hydroslide/tires_monitor/3d_parts/final parts/Power Input Box. lidstl.stl

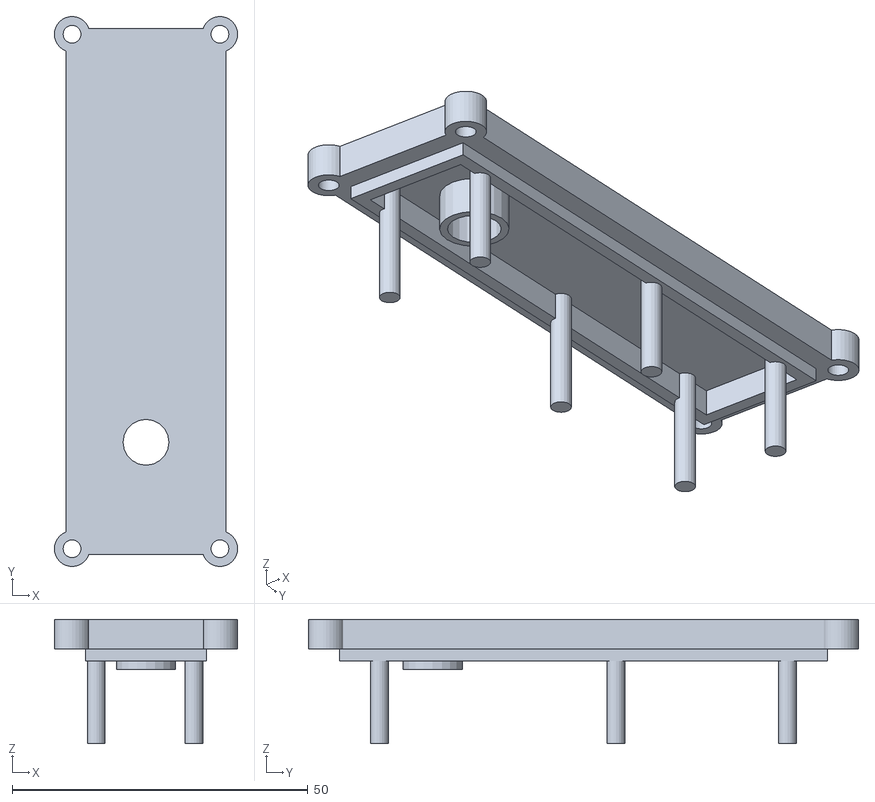
[picture p17: CAD file, 2025-01-14]
3d_parts/final parts/Power Input Box. lidstl.stl
31.0 x 93.0 x 21.0
