hydroslide/tires_monitor/3d_parts/final parts/display/Tire Temp Display Module high cup thick.stl

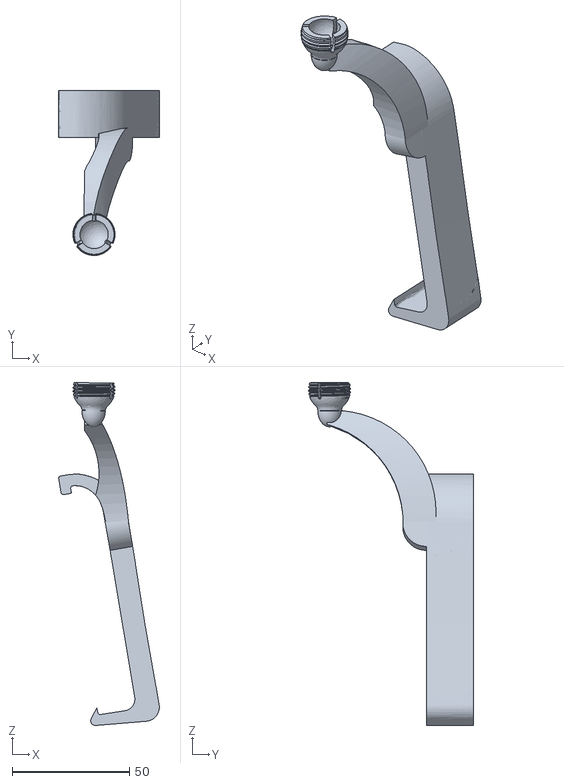
[picture p18: CAD file, 2025-01-14]
3d_parts/final parts/display/Tire Temp Display Module high cup thick.stl
42.9 x 70.4 x 146.2
