hydroslide/tires_monitor/3d_parts/final parts/Power Input Box button.stl

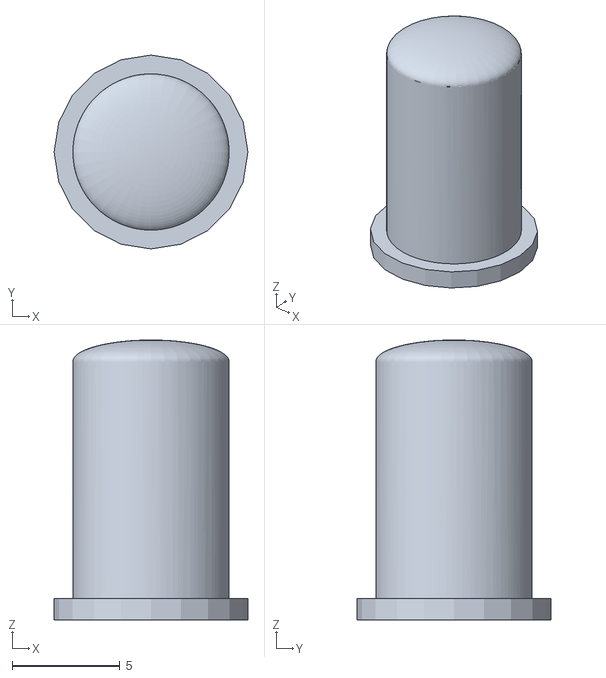
[picture p19: CAD file, 2025-01-14]
3d_parts/final parts/Power Input Box button.stl
9.00 x 9.00 x 13.0
