hydroslide/tires_monitor/3d_parts/final parts/display/Tire Temp Display Module ball.stl

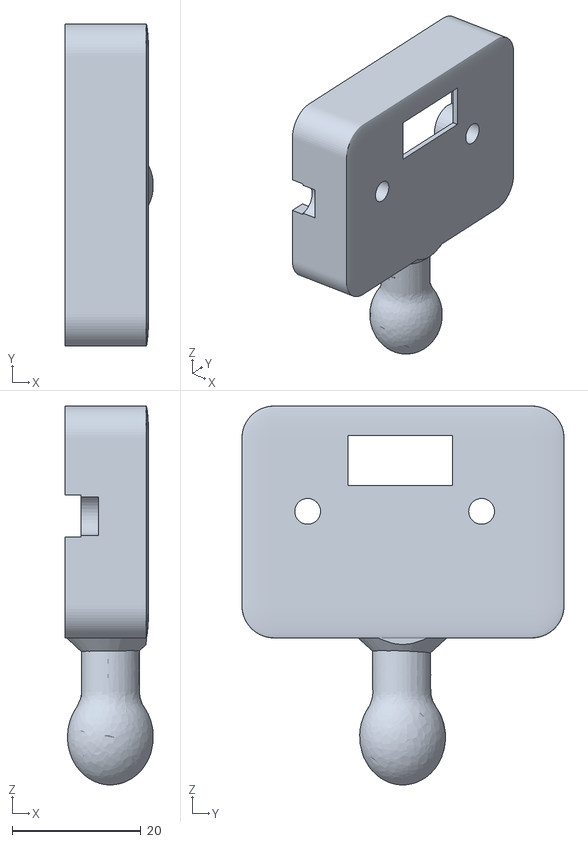
[picture p20: CAD file, 2025-01-14]
3d_parts/final parts/display/Tire Temp Display Module ball.stl
13.7 x 50.0 x 58.8
