hydroslide/tires_monitor/3d_parts/final parts/Tire Temp Sensor Box. protectionstl.stl

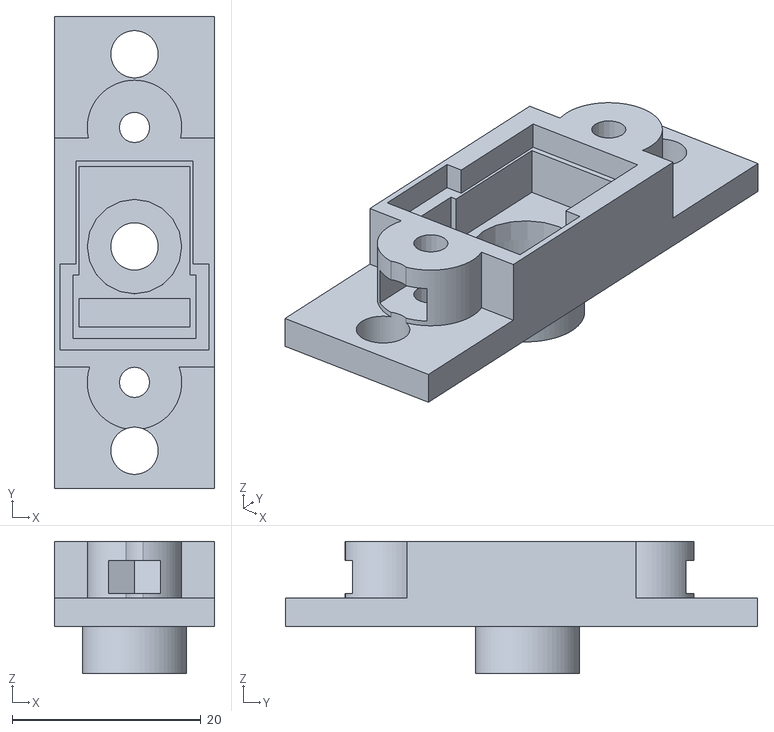
[picture p21: CAD file, 2025-01-14]
3d_parts/final parts/Tire Temp Sensor Box. protectionstl.stl
17.0 x 50.0 x 14.0
