hydroslide/tires_monitor/3d_parts/final parts/display/Tire Temp Display Module mount.stl

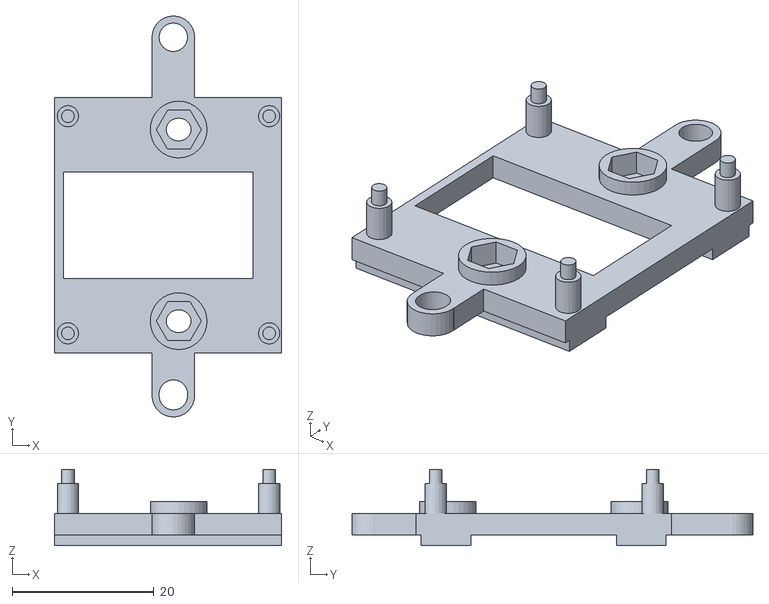
[picture p22: CAD file, 2025-01-14]
3d_parts/final parts/display/Tire Temp Display Module mount.stl
32.0 x 56.5 x 10.8
