hydroslide/tires_monitor/3d_parts/final parts/Tire Temp Sensor Lid.stl

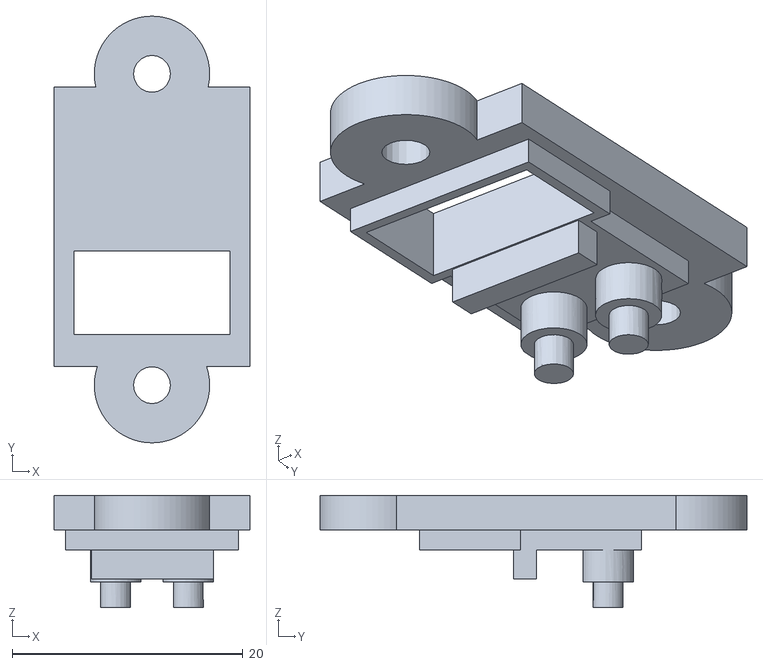
[picture p23: CAD file, 2024-12-06]
3d_parts/final parts/Tire Temp Sensor Lid.stl
17.0 x 37.0 x 9.75
