hydroslide/tires_monitor/3d_parts/final parts/display/Tire Temp Display Module ball mk2.stl

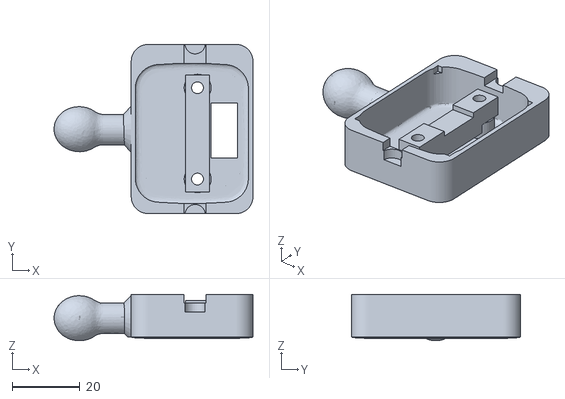
[picture p24: CAD file, 2025-01-14]
3d_parts/final parts/display/Tire Temp Display Module ball mk2.stl
58.8 x 50.0 x 13.7
