hydroslide/tires_monitor/3d_parts/final parts/display/Tire Temp Display Module strap new mk2.stl

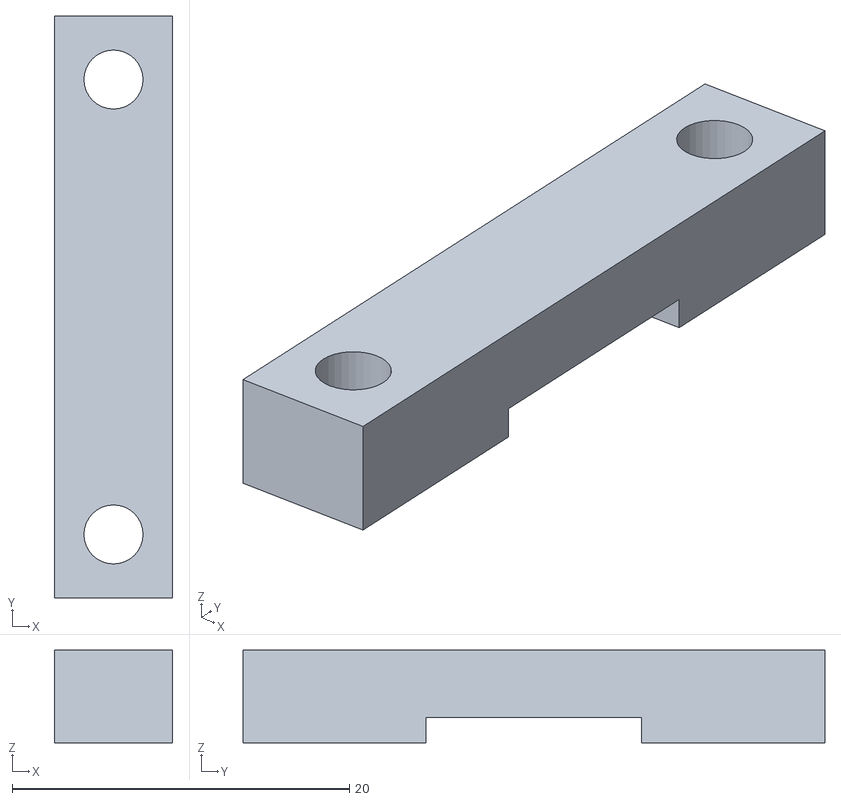
[picture p27: CAD file, 2025-01-14]
3d_parts/final parts/display/Tire Temp Display Module strap new mk2.stl
7.00 x 34.5 x 5.50
