hydroslide/tires_monitor/tires_esp32/Wheels.cpp

#include "Wheels.h"
#include "DisplayBase.h"
extern DisplayBase& display;

Wheels::Wheels(int _bufferPix,
               uint16_t _outlineColor,
               uint16_t _textColor,
               float _minTemp, float _idealTemp, float _maxTemp,
               char _tempUnit,
               bool _showSegmentDeltas, byte _minInflationDeltaPct, byte _minAlignmentDeltaPct,
               bool _fl3, bool _fr3, bool _rl3, bool _rr3,
               uint16_t _lowTempColor,    uint16_t _normalTempColor,
               uint16_t _idealTempColor,  uint16_t _highTempColor,
               uint16_t _lowTempTextColor,    uint16_t _normalTempTextColor,
               uint16_t _idealTempTextColor,  uint16_t _highTempTextColor)
  : bufferPix(_bufferPix), outlineColor(_outlineColor), textColor(_textColor),
    minTemp(_minTemp), idealTemp(_idealTemp), maxTemp(_maxTemp),
    tempUnit(_tempUnit),
    showSegmentDeltas(_showSegmentDeltas), minInflationDeltaPct(_minInflationDeltaPct), minAlignmentDeltaPct(_minAlignmentDeltaPct),
    fl3(_fl3), fr3(_fr3), rl3(_rl3), rr3(_rr3),
    lowTempColor(_lowTempColor), normalTempColor(_normalTempColor),
    idealTempColor(_idealTempColor), highTempColor(_highTempColor),
    lowTempTextColor(_lowTempTextColor), normalTempTextColor(_normalTempTextColor),
    idealTempTextColor(_idealTempTextColor), highTempTextColor(_highTempTextColor)
{
    int tireW  = (display.width()  - bufferPix*3) / 2;
    int tireH  = (display.height() - bufferPix*3) / 2;
    int x0 = bufferPix, x1 = x0 + tireW + bufferPix;
    int y0 = bufferPix, y1 = y0 + tireH + bufferPix;

    // lambda to pick class based on the bool
    auto mk = [&](bool three, int x, int y, byte index){
      if (three){
        ThreeSectionTire* tire = new ThreeSectionTire(x,y,tireW,tireH, bufferPix,
                                          outlineColor,textColor,tempUnit);
        tire->showSegmentDeltas = showSegmentDeltas;
        tire->minInflationDeltaPct = minInflationDeltaPct;
        tire->minAlignmentDeltaPct = minAlignmentDeltaPct;
        tire->tireIndex=index;
        return (Tire*)tire;
        }
      else
        return (Tire*)new Tire(x,y,tireW,tireH, bufferPix,
                               outlineColor,textColor,tempUnit);
    };

    frontLeft  = mk(fl3, x0,y0, 0);
    frontRight = mk(fr3, x1,y0, 1);
    rearLeft   = mk(rl3, x0,y1, 2);
    rearRight  = mk(rr3, x1,y1, 3);

    //   // Attempt to allocate frame buffer in PSRAM
    // framebuf = (uint16_t *)heap_caps_malloc(
    //     tft.width()* tft.height() * sizeof(uint16_t),
    //     MALLOC_CAP_SPIRAM
    // );
    // if (!framebuf) {
    //     // Fall back to normal heap
    //     framebuf = (uint16_t *)malloc(tft.width()* tft.height() * sizeof(uint16_t));
    // }
    // if (!framebuf) {
    //     // If allocation fails, halt
    //     while (true) { delay(1000); }
    // }


    // for (int yy = yStart; yy < yEnd; yy++) {
    //     for (int xx = xStart; xx < xEnd; xx++) {
    //         framebuf[yy * areaW + xx] = color;
    //     }
    //     // Yield to avoid watchdog reset
    //     //yield();
    // }
}

Wheels::Wheels(Wheels* src, bool _fl3, bool _fr3, bool _rl3, bool _rr3)
  : Wheels(
      src->bufferPix,
      src->outlineColor,
      src->textColor,
      src->minTemp, src->idealTemp, src->maxTemp,
      src->tempUnit,
      src->showSegmentDeltas, src->minInflationDeltaPct, src->minAlignmentDeltaPct,
      _fl3, _fr3, _rl3, _rr3,
      src->lowTempColor,
      src->normalTempColor,
      src->idealTempColor,
      src->highTempColor,
      src->lowTempTextColor,
      src->normalTempTextColor,
      src->idealTempTextColor,
      src->highTempTextColor
    )
{}

Wheels::~Wheels() {
    delete frontLeft;
    delete frontRight;
    delete rearLeft;
    delete rearRight;

    // if (framebuf) {
    //     free(framebuf);
    //     framebuf = nullptr;
    // }
}

void Wheels::draw(bool force, bool textOnly) {
    //RefreshScreen();
    if (flIsActive)
        frontLeft->draw(force, textOnly);
    if (frIsActive)
        frontRight->draw(force, textOnly);
    if (rlIsActive)        
        rearLeft->draw(force, textOnly);
    if (rrIsActive)
        rearRight->draw(force, textOnly);
}

void Wheels::RefreshScreen(){
        // Push the entire buffer to ST7789 at (areaX, areaY)
    // tft.startWrite();
    // tft.setAddrWindow(0, 0, tft.width(), tft.height());
    // tft.writePixels(framebuf, tft.width() * tft.height());
    // tft.endWrite();
}

void Wheels::setTireTemps(const TireTemps &fl,
                         const TireTemps &fr,
                         const TireTemps &rl,
                         const TireTemps &rr)
{
    struct P { Tire *t; const TireTemps &v; };
    P list[4] = {
      {frontLeft,  fl},
      {frontRight, fr},
      {rearLeft,   rl},
      {rearRight,  rr}
    };
    for (auto &p : list) {
      p.t->setTemps(p.v.values, p.v.count, (tempUnit=='F'),
                    minTemp, idealTemp, maxTemp,
                    lowTempColor, normalTempColor,
                    idealTempColor, highTempColor,
                    lowTempTextColor, normalTempTextColor,
                    idealTempTextColor, highTempTextColor);
    }
}

// Resolve a corner index to its ThreeSectionTire, or nullptr for a single-sensor corner.
// The fl3/fr3/rl3/rr3 flags stand in for RTTI, which this build doesn't have.
ThreeSectionTire* Wheels::cameraCorner(int corner) const {
    Tire* t;
    bool three;
    switch (corner) {
      case 0: t = frontLeft;  three = fl3; break;
      case 1: t = frontRight; three = fr3; break;
      case 2: t = rearLeft;   three = rl3; break;
      case 3: t = rearRight;  three = rr3; break;
      default: return nullptr;
    }
    return three ? static_cast<ThreeSectionTire*>(t) : nullptr;
}

void Wheels::setInflationVerdict(int corner, int8_t verdict) {
    ThreeSectionTire* ts = cameraCorner(corner);
    if (ts) ts->setInflationVerdict(verdict);
}

void Wheels::setDwellProgress(int corner, long score, long latch, long max) {
    ThreeSectionTire* ts = cameraCorner(corner);
    if (ts) ts->setDwellProgress(score, latch, max);
}

bool Wheels::cornerColors(int corner, uint16_t fill[3], uint16_t delta[3]) const {
    Tire* t;
    bool three;
    switch (corner) {
      case 0: t = frontLeft;  three = fl3; break;
      case 1: t = frontRight; three = fr3; break;
      case 2: t = rearLeft;   three = rl3; break;
      case 3: t = rearRight;  three = rr3; break;
      default: return false;
    }
    if (!three) return false;
    ThreeSectionTire* ts = static_cast<ThreeSectionTire*>(t);
    for (int i = 0; i < 3; i++) {
      fill[i]  = ts->sectionFillColor(i);
      delta[i] = ts->sectionDeltaColor(i);
    }
    return true;
}

    char Wheels::getTempUnit(){ return
     tempUnit;}
    void Wheels::setTempUnit(char _tempUnit){
        tempUnit=_tempUnit;
        frontLeft->tempUnit=tempUnit;
        frontRight->tempUnit=tempUnit;
        rearLeft->tempUnit=tempUnit;
        rearRight->tempUnit=tempUnit;
    }
