hydroslide/tires_monitor/tires_esp32/ThermalDisplay.cpp

#include "ThermalDisplay.h"
#include <esp_heap_caps.h>   // for heap_caps_malloc (PSRAM allocation)
#include <Arduino.h>         // for yield()
#include "TempReader.h"
#include <math.h>


extern HWCDC USBSerial;

// Define the static 256-entry color palette (RGB565)
const uint16_t ThermalDisplay::camColors[256] = {
  0x480F, 0x400F, 0x400F, 0x400F, 0x4010, 0x3810, 0x3810, 0x3810, 0x3810, 0x3010,
  0x3010, 0x3010, 0x2810, 0x2810, 0x2810, 0x2810, 0x2010, 0x2010, 0x2010, 0x1810,
  0x1810, 0x1811, 0x1811, 0x1011, 0x1011, 0x1011, 0x0811, 0x0811, 0x0811, 0x0011,
  0x0011, 0x0011, 0x0011, 0x0011, 0x0031, 0x0031, 0x0051, 0x0072, 0x0072, 0x0092,
  0x00B2, 0x00B2, 0x00D2, 0x00F2, 0x00F2, 0x0112, 0x0132, 0x0152, 0x0152, 0x0172,
  0x0192, 0x0192, 0x01B2, 0x01D2, 0x01F3, 0x01F3, 0x0213, 0x0233, 0x0253, 0x0253,
  0x0273, 0x0293, 0x02B3, 0x02D3, 0x02D3, 0x02F3, 0x0313, 0x0333, 0x0333, 0x0353,
  0x0373, 0x0394, 0x03B4, 0x03D4, 0x03D4, 0x03F4, 0x0414, 0x0434, 0x0454, 0x0474,
  0x0474, 0x0494, 0x04B4, 0x04D4, 0x04F4, 0x0514, 0x0534, 0x0534, 0x0554, 0x0554,
  0x0574, 0x0574, 0x0573, 0x0573, 0x0573, 0x0572, 0x0572, 0x0572, 0x0571, 0x0591,
  0x0591, 0x0590, 0x0590, 0x058F, 0x058F, 0x058F, 0x058E, 0x05AE, 0x05AE, 0x05AD,
  0x05AD, 0x05AD, 0x05AC, 0x05AC, 0x05AB, 0x05CB, 0x05CB, 0x05CA, 0x05CA, 0x05CA,
  0x05C9, 0x05C9, 0x05C8, 0x05E8, 0x05E8, 0x05E7, 0x05E7, 0x05E6, 0x05E6, 0x05E6,
  0x05E5, 0x05E5, 0x0604, 0x0604, 0x0604, 0x0603, 0x0603, 0x0602, 0x0602, 0x0601,
  0x0621, 0x0621, 0x0620, 0x0620, 0x0620, 0x0620, 0x0E20, 0x0E20, 0x0E40, 0x1640,
  0x1640, 0x1E40, 0x1E40, 0x2640, 0x2640, 0x2E40, 0x2E60, 0x3660, 0x3660, 0x3E60,
  0x3E60, 0x3E60, 0x4660, 0x4660, 0x4E60, 0x4E80, 0x5680, 0x5680, 0x5E80, 0x5E80,
  0x6680, 0x6680, 0x6E80, 0x6EA0, 0x76A0, 0x76A0, 0x7EA0, 0x7EA0, 0x86A0, 0x86A0,
  0x8EA0, 0x8EC0, 0x96C0, 0x96C0, 0x9EC0, 0x9EC0, 0xA6C0, 0xAEC0, 0xAEC0, 0xB6E0,
  0xB6E0, 0xBEE0, 0xBEE0, 0xC6E0, 0xC6E0, 0xCEE0, 0xCEE0, 0xD6E0, 0xD700, 0xDF00,
  0xDEE0, 0xDEC0, 0xDEA0, 0xDE80, 0xDE80, 0xE660, 0xE640, 0xE620, 0xE600, 0xE5E0,
  0xE5C0, 0xE5A0, 0xE580, 0xE560, 0xE540, 0xE520, 0xE500, 0xE4E0, 0xE4C0, 0xE4A0,
  0xE480, 0xE460, 0xEC40, 0xEC20, 0xEC00, 0xEBE0, 0xEBC0, 0xEBA0, 0xEB80, 0xEB60,
  0xEB40, 0xEB20, 0xEB00, 0xEAE0, 0xEAC0, 0xEAA0, 0xEA80, 0xEA60, 0xEA40, 0xF220,
  0xF200, 0xF1E0, 0xF1C0, 0xF1A0, 0xF180, 0xF160, 0xF140, 0xF100, 0xF0E0, 0xF0C0,
  0xF0A0, 0xF080, 0xF060, 0xF040, 0xF020, 0xF800
};

// ─── DEFINE & INITIALIZE STATICS ──────────────────────
// You can tweak these defaults, or rely on setTemperatureRange()
int ThermalDisplay::thresholdMin     = MINTEMP;
int ThermalDisplay::thresholdIdeal   = (MINTEMP + MAXTEMP) / 2;
int ThermalDisplay::thresholdMax     = MAXTEMP;

bool ThermalDisplay::useGradient = true;
bool ThermalDisplay::showPixelOffsets = false;

// Interactive crop-offset setup (#23); driven by OffsetSetup while that mode is up.
bool   ThermalDisplay::setupActive    = false;
int8_t ThermalDisplay::setupCorner    = -1;
bool   ThermalDisplay::setupRightSide = false;
bool   ThermalDisplay::setupBlinkOn   = true;
bool   ThermalDisplay::setupGuides    = true;   // cleared by LensSetup only (#31)

uint16_t ThermalDisplay::camPalette[256];
int      ThermalDisplay::lenCold;
int      ThermalDisplay::lenWarm;
int      ThermalDisplay::lenIdeal;
int      ThermalDisplay::lenHot;

// define+zero-init the static pointer:
uint16_t* ThermalDisplay::framebuf = nullptr;
TempReader* ThermalDisplay::tempReader = nullptr;

ThermalDisplay::ThermalDisplay(DisplayBase &displayTFT,
                               int areaX, int areaY,
                               int areaW, int areaH)
  : display(displayTFT),
    areaX(areaX), areaY(areaY), areaW(areaW), areaH(areaH)
{
    if (!framebuf){
        // Attempt to allocate frame buffer in PSRAM
        framebuf = (uint16_t *)heap_caps_malloc(
            areaW * areaH * sizeof(uint16_t),
            MALLOC_CAP_SPIRAM
        );
        if (!framebuf) {
            // Fall back to normal heap
            framebuf = (uint16_t *)malloc(areaW * areaH * sizeof(uint16_t));
        }
        if (!framebuf) {
            // If allocation fails, halt
            while (true) { delay(1000); }
        }
    }


}



ThermalDisplay::~ThermalDisplay() {
    if (framebuf) {
        free(framebuf);
        framebuf = nullptr;
    }
}

float ThermalDisplay::fahrenheitToCelsius(float f){
    return (f - 32.0f) * 5.0f / 9.0f;
}

// ─── STATIC THRESHOLD SETTER ──────────────────────────
void ThermalDisplay::setTemperatureRangeC(int minTemp,
                                         int idealTemp,
                                         int maxTemp)
{
    thresholdMin   = constrain(minTemp,   MINTEMP,   MAXTEMP);
    thresholdIdeal = constrain(idealTemp, thresholdMin, MAXTEMP);
    thresholdMax   = constrain(maxTemp,   thresholdIdeal, MAXTEMP);
    generatePalette();
}

void ThermalDisplay::setTemperatureRangeF(int minTemp,
                                         int idealTemp,
                                         int maxTemp)
{
    int minTempC = (int)fahrenheitToCelsius(minTemp);
    int idealTempC = (int)fahrenheitToCelsius(idealTemp);
    int maxTempC = (int)fahrenheitToCelsius(maxTemp);
    setTemperatureRangeC(minTempC, idealTempC, maxTempC);
}

/*
// ─── STATIC MAPPING HELPER ────────────────────────────
uint8_t ThermalDisplay::getColorIndexForTemp(int celsius) {
    // clamp within our class‐wide bounds
    celsius = constrain(celsius, thresholdMin, thresholdMax);

    // first half of palette = [thresholdMin…thresholdIdeal]
    if (celsius <= thresholdIdeal) {
        int upper = max(thresholdIdeal, thresholdMin + 1);
        int idx = map(celsius, thresholdMin, upper, 1, 127);
        return constrain(idx, 0, 127);
    }
    // second half        = (thresholdIdeal…thresholdMax]
    else {
        int lower = min(thresholdIdeal, thresholdMax - 1);
        int idx   = map(celsius, lower, thresholdMax, 128, 254);
        return constrain(idx, 128, 255);
    }
}
    */
uint8_t ThermalDisplay::getColorIndexForTemp(int c) {
    // clamp entire range: [min-7 … max+7]
    int lo = thresholdMin - 7;
    int hi = thresholdMax + 7;
    c = constrain(c, lo, hi);

    // pick which segment, then local map
    if (c <= thresholdMin) {
        // cold segment
        return map(c, lo, thresholdMin, 0, lenCold - 1);
    }
    else if (c <= thresholdIdeal) {
        // warm segment
        int start = lenCold;
        return start + map(c, thresholdMin, thresholdIdeal,
                           0, lenWarm - 1);
    }
    else if (c <= thresholdMax) {
        // ideal segment
        int start = lenCold + lenWarm;
        return start + map(c, thresholdIdeal, thresholdMax,
                           0, lenIdeal - 1);
    }
    else {
        // hot segment
        int start = lenCold + lenWarm + lenIdeal;
        return start + map(c, thresholdMax, hi,
                           0, lenHot - 1);
    }
}

static inline float _clamp360(float h) { 
  while (h < 0) h += 360.0f; 
  while (h >= 360.0f) h -= 360.0f; 
  return h; 
}

void ThermalDisplay::rgb2hsv(uint8_t R,uint8_t G,uint8_t B, float& h,float& s,float& v) {
  float r = R/255.0f, g = G/255.0f, b = B/255.0f;
  float maxv = fmaxf(r,fmaxf(g,b)), minv = fminf(r,fminf(g,b));
  v = maxv;
  float d = maxv - minv;
  s = (maxv == 0.0f) ? 0.0f : d / maxv;
  if (d == 0.0f) { h = 0.0f; return; }
  if (maxv == r)      h = 60.0f * fmodf(((g - b) / d), 6.0f);
  else if (maxv == g) h = 60.0f * (((b - r) / d) + 2.0f);
  else                h = 60.0f * (((r - g) / d) + 4.0f);
  if (h < 0) h += 360.0f;
}

void ThermalDisplay::hsv2rgb888(float h,float s,float v, uint8_t& R,uint8_t& G,uint8_t& B) {
  h = _clamp360(h);
  float c = v * s;
  float hh = (h / 60.0f);
  float x = c * (1.0f - fabsf(fmodf(hh, 2.0f) - 1.0f));
  float r=0,g=0,b=0;
  if      (0<=hh && hh<1){ r=c; g=x; b=0; }
  else if (1<=hh && hh<2){ r=x; g=c; b=0; }
  else if (2<=hh && hh<3){ r=0; g=c; b=x; }
  else if (3<=hh && hh<4){ r=0; g=x; b=c; }
  else if (4<=hh && hh<5){ r=x; g=0; b=c; }
  else                   { r=c; g=0; b=x; }
  float m = v - c;
  r += m; g += m; b += m;
  R = (uint8_t)lroundf(r*255.0f);
  G = (uint8_t)lroundf(g*255.0f);
  B = (uint8_t)lroundf(b*255.0f);
}

uint16_t ThermalDisplay::interpolateHSV_saturated(uint16_t c1, uint16_t c2, float t) {
  if (t <= 0.0f) return c1;
  if (t >= 1.0f) return c2;

  uint8_t r1,g1,b1, r2,g2,b2;
  rgb565_to_888(c1, r1,g1,b1);
  rgb565_to_888(c2, r2,g2,b2);

  float h1,s1,v1, h2,s2,v2;
  rgb2hsv(r1,g1,b1, h1,s1,v1);
  rgb2hsv(r2,g2,b2, h2,s2,v2);

  // shortest-path hue interpolation
  float dh = fmodf((h2 - h1 + 540.0f), 360.0f) - 180.0f; // [-180,180]
  float h  = _clamp360(h1 + t * dh);

  // fully saturated rim (S=1, V=1) inside band
  uint8_t R,G,B;
  hsv2rgb888(h, 1.0f, 1.0f, R,G,B);
  return rgb888_to_565(R,G,B);
}

uint16_t ThermalDisplay::interpolateDesaturateToTarget(uint16_t cStart, uint16_t cEnd, float t) {
  if (t <= 0.0f) return cStart;
  if (t >= 1.0f) return cEnd;

  uint8_t rs,gs,bs, re,ge,be;
  rgb565_to_888(cStart, rs,gs,bs);
  rgb565_to_888(cEnd,   re,ge,be);

  float hs,ss,vs, he,se,ve;
  rgb2hsv(rs,gs,bs, hs,ss,vs);
  rgb2hsv(re,ge,be, he,se,ve);

  // hold hue at start, ramp S: 1 → se, and V: vs → ve
  float s = 1.0f + (se - 1.0f) * t;
  float v = vs    + (ve - vs)  * t;

  uint8_t R,G,B;
  hsv2rgb888(hs, s, v, R,G,B);
  return rgb888_to_565(R,G,B);
}

/*
void ThermalDisplay::generatePalette() {
    // 1/8th for “hot” (red→white) = 32 entries
    lenHot = 256 / 8;       // = 32
    int rest = 256 - lenHot; // = 224

    // degree spans
    int spanCold = 7;                         // fixed
    int spanWarm = thresholdIdeal - thresholdMin;
    int spanIdeal= thresholdMax   - thresholdIdeal;
    int sumRest = spanCold + spanWarm + spanIdeal;

    // allocate the other three segment lengths proportionally
    lenCold  = max(1, int(round((float)spanCold  / sumRest * rest)));
    lenWarm  = max(1, int(round((float)spanWarm  / sumRest * rest)));
    // ensure we fill exactly 'rest'
    lenIdeal = rest - lenCold - lenWarm;

    // now carve into camPalette[]
    int idx = 0;

    // ── cold: violet → cyan
    for (int i = 0; i < lenCold; ++i) {
        float t = float(i) / (lenCold - 1);
        if (useGradient)
            camPalette[idx++] = interpolate565(COLOR_COLD_START, COLOR_CYAN, t);
        else
            camPalette[idx++] = COLOR_COLD;
    }
    // ── warm: cyan → yellow-orange
    for (int i = 0; i < lenWarm; ++i) {
        float t = float(i) / (lenWarm - 1);
        if (useGradient)
            camPalette[idx++] = interpolate565(COLOR_CYAN, COLOR_ORANGE, t);// COLOR_YELLOW_ORANGE, t);
        else
            camPalette[idx++] = COLOR_WARM;
    }
    // ── ideal: yellow-orange → red
    int lastI = 0;
    int halfIdeal = lenIdeal/2;
    for (int i = 0; i < halfIdeal; ++i) {
        float t = float(i) / (halfIdeal - 1);
        if (useGradient)
            camPalette[idx++] = interpolate565(COLOR_ORANGE, COLOR_PURPLE, t);//interpolate565(COLOR_YELLOW_ORANGE, COLOR_RED, t);
        else
            camPalette[idx++] = COLOR_PURPLE;//COLOR_IDEAL;
    }

    halfIdeal = lenIdeal-halfIdeal;
    for (int i =0; i < halfIdeal; ++i) {
        float t = float(i) / (halfIdeal - 1);
        if (useGradient)
            camPalette[idx++] = interpolate565(COLOR_PURPLE, COLOR_PURPLE_HOT, t);//interpolate565(COLOR_YELLOW_ORANGE, COLOR_RED, t);
        else
            camPalette[idx++] = COLOR_PURPLE;//COLOR_IDEAL;
    }


    // ── hot: red → white (always 32 entries)
    for (int i = 0; i < lenHot; ++i) {
        float t = float(i) / (lenHot - 1);
        if (useGradient)
            camPalette[idx++] = interpolate565(COLOR_PURPLE_HOT, COLOR_HOT, t); //interpolate565(COLOR_RED, COLOR_WHITE, t);
        else
            camPalette[idx++] = COLOR_HOT;
    }
}
    */

void ThermalDisplay::generatePalette() {
  // 1/8th for “hot” tail
  lenHot = 256 / 8;                 // 32
  int rest = 256 - lenHot;          // 224

  // degree spans (unchanged)
  int spanCold  = 7;
  int spanWarm  = thresholdIdeal - thresholdMin;
  int spanIdeal = thresholdMax   - thresholdIdeal;
  int sumRest   = spanCold + spanWarm + spanIdeal;

  lenCold  = max(1, int(lroundf((float)spanCold  / sumRest * rest)));
  lenWarm  = max(1, int(lroundf((float)spanWarm  / sumRest * rest)));
  lenIdeal =           rest - lenCold - lenWarm;

  auto t_of = [](int i, int n) -> float {
    return (n > 1) ? (float)i / (float)(n - 1) : 0.0f;
  };

  int idx = 0;

  // COLD: violet → cyan (HSV saturated)
  for (int i = 0; i < lenCold; ++i) {
    float t = t_of(i, lenCold);
    camPalette[idx++] = useGradient
      ? interpolateHSV_saturated(COLOR_COLD_START, COLOR_CYAN, t)
      : COLOR_COLD;
  }

  // WARM: cyan → orange (HSV saturated)
  for (int i = 0; i < lenWarm; ++i) {
    float t = t_of(i, lenWarm);
    camPalette[idx++] = useGradient
      ? interpolateHSV_saturated(COLOR_CYAN, COLOR_ORANGE, t)
      : COLOR_WARM;
  }

  // IDEAL (split in half, as you already do):
  //   orange → purple (HSV saturated)
  int halfIdealA = lenIdeal / 2;
  for (int i = 0; i < halfIdealA; ++i) {
    float t = t_of(i, halfIdealA);
    camPalette[idx++] = useGradient
      ? interpolateHSV_saturated(COLOR_ORANGE, COLOR_PURPLE, t)
      : COLOR_PURPLE; // your solid fallback
  }

  //   purple → purple_hot (HSV saturated)
  int halfIdealB = lenIdeal - halfIdealA;
  for (int i = 0; i < halfIdealB; ++i) {
    float t = t_of(i, halfIdealB);
    camPalette[idx++] = useGradient
      ? interpolateHSV_saturated(COLOR_PURPLE, COLOR_PURPLE_HOT, t)
      : COLOR_PURPLE; // your solid fallback
  }

  // HOT: purple_hot → hot (desaturate toward your target color)
  for (int i = 0; i < lenHot; ++i) {
    float t = t_of(i, lenHot);
    camPalette[idx++] = useGradient
      ? interpolateDesaturateToTarget(COLOR_PURPLE_HOT, COLOR_HOT, t)
      : COLOR_HOT;
  }

  // Safety: ensure we filled exactly 256
  // (harmless if idx==256; clamps if rounding created an off-by-one)
  while (idx < 256) camPalette[idx++] = camPalette[255];
}


uint16_t ThermalDisplay::interpolate565(uint16_t c1,
                                        uint16_t c2,
                                        float t)
{
    // extract 5/6/5 bits
    int r1 = (c1 >> 11) & 0x1F,  g1 = (c1 >> 5) & 0x3F,  b1 = c1 & 0x1F;
    int r2 = (c2 >> 11) & 0x1F,  g2 = (c2 >> 5) & 0x3F,  b2 = c2 & 0x1F;
    // linear interp
    int r = r1 + (r2 - r1) * t + 0.5f;
    int g = g1 + (g2 - g1) * t + 0.5f;
    int b = b1 + (b2 - b1) * t + 0.5f;
    // re-pack
    return (uint16_t)((r << 11) | (g << 5) | b);
}


void ThermalDisplay::setTempIndex(int _tempIndex){                                        
        tempIndex = _tempIndex;
    }

void ThermalDisplay::updateDisplay(){
   updateDisplay(tempIndex);
}

void ThermalDisplay::updateDisplay(int _tempIndex){
     if (isActive && tempReader->tireSensorIsCamera[_tempIndex])
        updateDisplay(tempReader->tire_frames[_tempIndex], _tempIndex);
}

/*
void ThermalDisplay::updateDisplay(const int temps[CAMERA_WIDTH * CAMERA_HEIGHT], int _tempIndex)
{
    // Build the areaW×areaH RGB565 buffer from 32×24 temps[]
    for (int camY = 0; camY < CAMERA_HEIGHT; camY++) {
        for (int camX = 0; camX < CAMERA_WIDTH; camX++) {
            int idxFlat = camY * CAMERA_WIDTH + camX;

            int raw = temps[idxFlat];
            // clamp using our static min/max
            //raw = constrain(raw, thresholdMin, thresholdMax);

            uint8_t ci      = getColorIndexForTemp(raw);
            uint16_t color  = camPalette[ci];//camColors[ci];
           
            // Compute scaled block in areaW×areaH
            int xStart = (camX     * areaW) / CAMERA_WIDTH;
            int xEnd   = ((camX+1) * areaW) / CAMERA_WIDTH;
            int yStart = (camY     * areaH) / CAMERA_HEIGHT;
            int yEnd   = ((camY+1) * areaH) / CAMERA_HEIGHT;

            for (int yy = yStart; yy < yEnd; yy++) {
                for (int xx = xStart; xx < xEnd; xx++) {
                    framebuf[yy * areaW + xx] = color;
                }
                // Yield to avoid watchdog reset
                //yield();
            }
        }
    }

    // Push the entire buffer to display at (areaX, areaY)
    display.pushPixels(areaX, areaY, areaW, areaH, framebuf, areaW * areaH);

    if (showPixelOffsets)
        drawPixelOffsets(_tempIndex);
}
*/

void ThermalDisplay::updateDisplay(const int temps[CAMERA_WIDTH * CAMERA_HEIGHT], int _tempIndex)
{
    // When showPixelOffsets == false, we *stretch* only the X range between the two offsets
    // to fill the entire display width. Y mapping is unchanged.
    int leftOff  = 0;
    int rightOff = 0;
    int cropW    = CAMERA_WIDTH;
    // Offset setup (#23) always shows the FULL frame regardless of the Show Offsets setting:
    // a guide drawn over an image that has already been cropped to those same offsets is a
    // line down the edge of the screen saying nothing. You can only aim a crop against the
    // uncropped picture.
    const bool stretchX = !showPixelOffsets && !setupActive;

    if (stretchX) {
        // Read the per-sensor offsets
        leftOff  = (int)tempReader->leftPixelOffset[_tempIndex];
        rightOff = (int)tempReader->rightPixelOffset[_tempIndex];

        // Sanity checks to avoid degenerate/invalid ranges
        if (leftOff   < 0) leftOff = 0;
        if (rightOff  < 0) rightOff = 0;
        if (leftOff + rightOff >= CAMERA_WIDTH) { // pathological; disable stretch
            leftOff = 0; rightOff = 0;
        }
        cropW = CAMERA_WIDTH - leftOff - rightOff;
        if (cropW <= 0) cropW = 1; // hard guard against div-by-zero
    }

    // Build the areaW×areaH RGB565 buffer from 32×24 temps[]
    for (int camY = 0; camY < CAMERA_HEIGHT; camY++) {
        // Y scaling is unchanged regardless of stretch
        const int yStart = (camY     * areaH) / CAMERA_HEIGHT;
        const int yEnd   = ((camY+1) * areaH) / CAMERA_HEIGHT;

        // X loop: either full width or the cropped range
        const int xBegin = stretchX ? leftOff : 0;
        const int xFinal = CAMERA_WIDTH - (stretchX ? rightOff : 0);

        for (int camX = xBegin; camX < xFinal; camX++) {
            const int idxFlat = camY * CAMERA_WIDTH + camX;

            // A pixel the lens correction has no source data for is painted BLACK, never
            // run through the palette (#31). getColorIndexForTemp() clamps its input into
            // the threshold range, so every possible int comes back as a real temperature
            // colour -- a placeholder value would render as a confident reading. Cold-end
            // navy would read as "cold background"; hot-end (0xFF9F, near-white) would
            // read as a scorching tire. Black is already this display's "nothing here"
            // (it is what a corner with no camera shows), and it is in no palette.
            uint16_t color;
            if (!TempReader::lensPixelValid(idxFlat)) {
                color = ST77XX_BLACK;
            } else {
                int raw = temps[idxFlat];
                uint8_t ci = getColorIndexForTemp(raw);
                color = camPalette[ci];
            }

            // Compute scaled block in areaW×areaH
            // If stretching, remap localX (camX - leftOff) across cropW → full areaW.
            // If not stretching, localX == camX and cropW == CAMERA_WIDTH (original behavior).
            const int localX = stretchX ? (camX - leftOff) : camX;

            const int xStart = (localX     * areaW) / cropW;
            const int xEnd   = ((localX+1) * areaW) / cropW;

            for (int yy = yStart; yy < yEnd; yy++) {
                uint16_t* row = &framebuf[yy * areaW];
                for (int xx = xStart; xx < xEnd; xx++) {
                    row[xx] = color;
                }
            }
        }
    }

    // Push the entire buffer to display at (areaX, areaY)
    display.pushPixels(areaX, areaY, areaW, areaH, framebuf, areaW * areaH);

    // When not stretching (i.e., showPixelOffsets == true, or offset setup owns the screen),
    // draw the guide lines on top. setupGuides is the one exception: Set Camera Degrees
    // (#31) borrows setupActive for its full-frame view but wants no guides over it.
    if ((showPixelOffsets || setupActive) && setupGuides)
        drawPixelOffsets(_tempIndex);
}


void ThermalDisplay::drawPixelOffsets(int _tempIndex){
    byte leftOffset = tempReader->leftPixelOffset[_tempIndex];
    byte rightOffset = tempReader->rightPixelOffset[_tempIndex];

    // Setup mode draws BOTH guides unconditionally (#23). Outside it the >0 guard stays: a
    // zero-offset guide lands hard against the image edge and is just clutter when nobody is
    // aiming the camera. While aiming it is the opposite -- an invisible line is one you
    // cannot walk back out from zero.
    const bool always = setupActive;

    // Which guide, if either, is the value being edited. -1 means nothing is armed (the
    // confirm screens), so every line sits steady.
    const bool armedHere = setupActive && (setupCorner == (int8_t)_tempIndex);

    if(leftOffset >0 || always){
        int leftX = (((leftOffset * areaW) / CAMERA_WIDTH)-1)+areaX;
        drawOffsetGuide(leftX, armedHere && !setupRightSide);
    }

    if (rightOffset >0 || always){
        int rightX = ((areaW- ((rightOffset * areaW) / CAMERA_WIDTH))+1)+areaX;
        drawOffsetGuide(rightX, armedHere && setupRightSide);
    }

}

// One crop guide.
//
// Every pixel is clamped into the image rectangle, because that rectangle -- and only that
// rectangle -- is re-blitted on the next update. A line drawn in the bezel margin (which is
// where the arithmetic above puts a 0 offset) would never be erased, so it would smear as
// the value moved and the blink would have nothing to blink against.
void ThermalDisplay::drawOffsetGuide(int x, bool armed){
    const int lo = areaX;
    const int hi = areaX + areaW - 1;

    if (x < lo) x = lo;
    if (x > hi) x = hi;

    // The dark half of the blink draws nothing at all: the next frame's blit is the erase,
    // so there is no second color to paint and no flicker in the image underneath.
    if (armed && !setupBlinkOn) return;

    // The armed guide is 3 px wide so it is unmistakable at arm's length in daylight -- it
    // is the only thing on screen saying which of the eight values a swipe will move.
    const int half = armed ? 1 : 0;
    for (int gx = x - half; gx <= x + half; gx++){
        if (gx >= lo && gx <= hi)
            display.drawFastVLine(gx, areaY, areaH, OFFSET_LINE_COLOR);
    }
}
