hydroslide/tires_monitor/tires_esp32/TireMenu.cpp

#include "TireMenu.h"
#include "MenuRenderer.h"
#include "TireProfiles.h"
#include "TempReader.h"
#include "OffsetSetup.h"
#include "LensSetup.h"

extern MenuRenderer menuRenderer;
// The live reader, owned by the sketch. Only "Set Offsets" (#23) and "Set Camera Degrees"
// (#31) read it here, and only to ask whether any corner has a camera worth aiming.
extern TempReader* tempReader;

// ----------------------------------------------------
//  1) Global variables for each setting
// ----------------------------------------------------

//
// -- Enums --
static uint8_t currentMode = 0; // 0=Street, 1=Track
static const char* currentModeLabels[] = {"Street", "Track"};

static uint8_t temperatureScale = 0; // 0=Farenheit, 1=Celsius
static const char* tempScaleLabels[] = {"F", "C"};

static uint8_t nightBrightness   = 25;

// -- Per-mode default tire profile (#14) --
// A mode no longer carries its own temp window; it names the tire profile it starts from,
// and the profile is the single source of truth for Min/Ideal/Max (plus K / tau / crop).
// Both are enum indices into the profile slots: Street -> EC02 (1), Track -> ECF (0).
static uint8_t streetProfile = 1;
static uint8_t trackProfile  = 0;

// -- Street tire temp window (#27) --
// Street gets its own Min/Ideal/Max back, and in Street mode it OVERRIDES the active
// profile's window. #14 was right that two windows for the same tire is redundant on
// track -- but street is not the same tire problem. A street window is not a tuning
// target, it is a "are these anywhere near warm" scale, and it has to stay put while you
// swap between profiles that are all tuned for track heat. Pinning it to a profile meant
// either editing that profile's window (breaking it for track) or keeping a decoy
// "street" profile whose K/tau/crop you did not actually want.
//
// So this overrides ONLY the window. K, tau and the camera crop offsets still come from
// the active profile in both modes -- nothing else carries them -- which is why the
// Street "Default Profile" above still matters in Street mode.
//
// The values are the pre-#14 Street window, unchanged: 40/120/160 in the same F-seed
// convention TireProfile.window* uses (stored as F, displayed/converted per Temperature
// Scale). Track is untouched and still reads the profile.
//
// Off is a real position: it falls straight back to the active profile's window, which is
// exactly the post-#14 behavior, so this can be A/B'd against the profile without
// retyping the numbers.
static bool    streetWindowEnabled = true;
static uint8_t streetMin           = 40;
static uint8_t streetIdeal         = 120;
static uint8_t streetMax           = 160;

// -- Calculated display mode (story 03; Track-mode only) --
// 0=Raw surface, 1=Calculated (EMA_tau(surface)+K carcass estimate).
static uint8_t calcDisplayMode = 0;
static const char* calcDisplayModeLabels[] = {"Raw", "Calculated"};

// -- Balance summary show/hide (story 05; Track-mode only) --
// Governs whether the front/rear + left/right balance readout is offered. When off the
// "Balance" summary item reports that it is hidden instead of opening.
static bool showBalance = true;

// -- Auto-seal on stationary (story 01; Track-mode only) --
// When on, a running session self-seals after a sustained still period (a backstop for
// a forgotten swipe-to-end). Best-effort IMU-stillness only (no speed channel), so it
// defaults off.
static bool autoSealStationary = false;

// -- Hardware Temp Sensor Indices -- REMOVED (#22)
// Four menu-editable, EEPROM-persisted bytes (addrs 20/22/24/26) that nothing ever read:
// there was no getter, and the real mux map is the hardcoded sensorIndices{0, 7, 3, 4} in
// TempReader's constructor. They presented as a working sensor remap and were not one, so
// the whole "Hardware Settings" branch went with them. The addresses are simply no longer
// walked by save/load; the stale bytes are inert, which is why this needed no magic bump.

// -- Camera Offsets --
// Per-corner crop offsets are no longer globals (#15): they live in TireProfile, are
// edited under Tire Profiles -> Offsets, and are read back through the accessors at the
// bottom of this file. "Camera Settings" keeps only the device-wide display toggles.

static bool useThermalGradient = true;
static bool testEnabled = true;
static bool showPixelOffsets = true;
static bool highFrequencyUpdates = false;

// -- Fisheye lens correction (#31) --
// Device-wide, not per-profile: this describes the LENS, one rig with four identical
// ones, so it has nothing to do with which tire is fitted.
//
// lensFovDegrees is the field of view across the 32-pixel width, fed straight into the
// re-projection. 110 is the wide-angle MLX90640's datasheet figure and the right place to
// start, but the real lens is not exactly equidistant -- which is why the value is tunable
// from the car via "Set Camera Degrees" rather than being a constant.
//
// lensFitToView chooses what happens to the rows the correction has no data for: off
// letterboxes them black (honest, and it shows you what the correction is costing), on
// squashes the image vertically to fill the frame (keeps lines straight, drops aspect
// ratio). Defaults OFF so the cost is visible while you are still finding the FOV.
static bool    lensCorrectEnabled = true;
static uint8_t lensFovDegrees     = 110;
static bool    lensFitToView      = false;
static bool showSegmentDeltas = false;
static uint8_t minInflationDeltaPct = 10;
static uint8_t minAlignmentDeltaPct = 15;

// -- IMU capture gate (global; story 02) --
// Two dwells live here and they are NOT the same thing (#20):
//   gateDwellTenths  -- how long the car must hold sub-threshold lateral g before we
//                       start CAPTURING. 0 reproduces the pre-#20 instant behavior.
//   alertDwellTenths -- how long an over/under condition must persist on already-captured
//                       frames before the inflation verdict LATCHES.
static bool    imuGateEnabled       = true; // suppress reads while cornering
static bool    showGateBar          = true; // on-screen lateral-g test bar (#20)
static uint8_t lateralGateCentiG    = 35;   // |lateral g| threshold, centi-g (0.35 g)
static uint8_t gateDwellTenths      = 5;    // capture dwell, tenths of a second (0.5 s)
static uint8_t alertDwellTenths     = 25;   // latch dwell, tenths of a second (2.5 s)
static uint8_t imuOrient            = 0;    // lateral-axis map: 0=Auto,1=X,2=Y,3=Z
static const char* imuOrientLabels[] = {"Auto", "X", "Y", "Z"};


// ----------------------------------------------------
//  2) MenuValueBindings
// ----------------------------------------------------
static MenuValueBinding currentModeBinding = {
    VALUE_ENUM,
    &currentMode,
    nullptr,
    0, // minByte
    0, // maxByte
    0, // eepromAddress (or -1 if ignoring)
    currentModeLabels,
    2  // enumCount
};

static MenuValueBinding temperatureScaleBinding = {
    VALUE_ENUM,
    &temperatureScale,
    nullptr,
    0,
    0,
    2, // eepromAddress or -1
    tempScaleLabels,
    2
};

// Night Brightenss
static MenuValueBinding nightBrightnessBinding = {
    VALUE_BYTE,
    &nightBrightness,
    nullptr,
    0,
    100,
    28,
    nullptr,
    0
};

// Per-mode default tire profile (#14). Persisted at two of the addresses freed by the
// removed Street/Track Min/Ideal/Max bytes (6 and 8); the rest (10, 14, 16, 18) were free
// until #27 claimed all four (see below). The labels are the live profile slot names, so
// renaming a profile renames the choices here too.
static MenuValueBinding streetProfileBinding = {
    VALUE_ENUM,
    &streetProfile,
    nullptr,
    0,
    0,
    6,
    g_profileNameLabels,
    PROFILE_COUNT
};

static MenuValueBinding trackProfileBinding = {
    VALUE_ENUM,
    &trackProfile,
    nullptr,
    0,
    0,
    8,
    g_profileNameLabels,
    PROFILE_COUNT
};

// Street tire temp window (#27). These reclaim the last four bytes #14 freed: 10 was the
// old streetMax, 14/16/18 the old trackMin/Ideal/Max. Reusing them is safe only because
// SETTINGS_MAGIC is bumped alongside -- a block saved by #14..#26 firmware never WROTE
// these four, so they still hold whatever a pre-#14 save left there, and
// loadMenuFromEEPROMHelper() copies bytes in verbatim with no min/max clamping. Without
// the bump a stale trackMax=180 at 18 would load as streetWindowEnabled=true and a stale
// trackMin=100 at 14 as the Street ideal. See MenuSystem.cpp.
//
// Same 0..255 range as the profile window fields: the window is a raw F-seed byte, and
// clamping min <= ideal <= max is the display's job (ThermalDisplay::setTemperatureRangeC),
// not the menu's -- so the ordering rule stays in exactly one place.
static MenuValueBinding streetWindowEnabledBinding = {
    VALUE_BOOL,
    &streetWindowEnabled,
    nullptr,
    0,
    0,
    18,
    nullptr,
    0
};

static MenuValueBinding streetMinBinding = {
    VALUE_BYTE,
    &streetMin,
    nullptr,
    0,
    255,
    10,
    nullptr,
    0
};

static MenuValueBinding streetIdealBinding = {
    VALUE_BYTE,
    &streetIdeal,
    nullptr,
    0,
    255,
    14,
    nullptr,
    0
};

static MenuValueBinding streetMaxBinding = {
    VALUE_BYTE,
    &streetMax,
    nullptr,
    0,
    255,
    16,
    nullptr,
    0
};

// Calculated display mode (EEPROM addr 1; free byte, magic-sentinel load makes 0 safe)
static MenuValueBinding calcDisplayModeBinding = {
    VALUE_ENUM,
    &calcDisplayMode,
    nullptr,
    0,
    0,
    1,
    calcDisplayModeLabels,
    2
};

// Balance summary show/hide (EEPROM addr 49; free byte between the menu bindings and
// the tire-profile region at 50+). The magic-sentinel load makes the false/0 case safe.
static MenuValueBinding showBalanceBinding = {
    VALUE_BOOL,
    &showBalance,
    nullptr,
    0,
    0,
    49,
    nullptr,
    0
};

// Auto-seal on stationary (EEPROM addr 3; free byte among the menu bindings). The
// magic-sentinel load makes the false/0 case safe.
static MenuValueBinding autoSealStationaryBinding = {
    VALUE_BOOL,
    &autoSealStationary,
    nullptr,
    0,
    0,
    3,
    nullptr,
    0
};

static MenuValueBinding useThermalGradientBinding = {
    VALUE_BOOL,
    &useThermalGradient,
    nullptr,
    0,
    0,
    30,
    nullptr,
    0
};

// EEPROM 31..38 used to hold the eight global camera offsets. #15 moved the offsets into
// the tire profile (persisted verbatim in the profile region), so 31 was re-purposed for
// the inflation indicator (see below) and 32..38 are now free.

static MenuValueBinding showPixelOffsetsBinding = {
    VALUE_BOOL,
    &showPixelOffsets,
    nullptr,
    0,
    0,
    39,
    nullptr,
    0
};

// Lens correction (#31). EEPROM 34/35/36, out of the run of bytes #15 freed and #20 took
// 32/33 from. No earlier firmware ever WROTE these, and loadMenuFromEEPROMHelper() copies
// stored bytes in verbatim with no min/max clamping -- a stale 0xFF at 34 would land as a
// 255-degree field of view and build a degenerate map on the first boot. SETTINGS_MAGIC is
// bumped alongside so the block re-seeds from the compiled-in defaults instead.
static MenuValueBinding lensCorrectEnabledBinding = {
    VALUE_BOOL,
    &lensCorrectEnabled,
    nullptr,
    0,
    0,
    35,
    nullptr,
    0
};
static MenuValueBinding lensFovDegreesBinding = {
    VALUE_BYTE,
    &lensFovDegrees,
    nullptr,
    60,    // below this the correction is doing nothing worth the resample
    140,   // above this the centre is de-magnified >2.2x and a fifth of the frame is dead;
           // the map degenerates entirely at 180 (rectilinear focal length -> 0)
    34,
    nullptr,
    0
};
static MenuValueBinding lensFitToViewBinding = {
    VALUE_BOOL,
    &lensFitToView,
    nullptr,
    0,
    0,
    36,
    nullptr,
    0
};

static MenuValueBinding testEnabledBinding = {
    VALUE_BOOL,
    &testEnabled,
    nullptr,
    0,
    0,
    40,
    nullptr,
    0
};
static MenuValueBinding highFrequencyUpdatesBinding = {
    VALUE_BOOL,
    &highFrequencyUpdates,
    nullptr,
    0,
    0,
    41,
    nullptr,
    0
};
static MenuValueBinding showSegmentDeltasBinding = {
    VALUE_BOOL,
    &showSegmentDeltas,
    nullptr,
    0,
    0,
    42,
    nullptr,
    0
};

static MenuValueBinding minInflationDeltaPctBinding = {
    VALUE_BYTE,
    &minInflationDeltaPct,
    nullptr,
    0,
    16,
    43,
    nullptr,
    0
};
static MenuValueBinding minAlignmentDeltaPctBinding = {
    VALUE_BYTE,
    &minAlignmentDeltaPct,
    nullptr,
    0,
    16,
    44,
    nullptr,
    0
};

// IMU capture gate test bar + capture dwell (#20). These take EEPROM 32 and 33 out of the
// run of bytes #15 freed. Because no earlier firmware ever WROTE 32/33, a stored settings
// block from before #20 holds junk there, and loadMenuFromEEPROMHelper() copies bytes in
// verbatim with no min/max clamping -- a stale 0xFF would land as a 25.5 s capture dwell.
// SETTINGS_MAGIC is bumped alongside this so the first boot after the flash re-seeds from
// the compiled-in defaults instead.
static MenuValueBinding gateDwellTenthsBinding = {
    VALUE_BYTE,
    &gateDwellTenths,
    nullptr,
    0,    // 0.0 s -- instant capture, the pre-#20 behavior
    50,   // 5.0 s
    32,
    nullptr,
    0
};
static MenuValueBinding showGateBarBinding = {
    VALUE_BOOL,
    &showGateBar,
    nullptr,
    0,
    0,
    33,
    nullptr,
    0
};

// IMU capture gate settings (EEPROM 45..48; magic-sentinel load makes 0 safe)
static MenuValueBinding imuGateEnabledBinding = {
    VALUE_BOOL,
    &imuGateEnabled,
    nullptr,
    0,
    0,
    45,
    nullptr,
    0
};
static MenuValueBinding lateralGateCentiGBinding = {
    VALUE_BYTE,
    &lateralGateCentiG,
    nullptr,
    10,   // 0.10 g
    100,  // 1.00 g
    46,
    nullptr,
    0
};
static MenuValueBinding alertDwellTenthsBinding = {
    VALUE_BYTE,
    &alertDwellTenths,
    nullptr,
    5,    // 0.5 s
    100,  // 10 s
    47,
    nullptr,
    0
};
static MenuValueBinding imuOrientBinding = {
    VALUE_ENUM,
    &imuOrient,
    nullptr,
    0,
    0,
    48,
    imuOrientLabels,
    4
};

// EEPROM 31 is FREE again as of #21, which removed the "Inflation" toggle. No magic bump
// is needed for a removal alone: no binding reads 31 any more, so a stale byte there is
// simply never loaded. Bump only if something later CLAIMS 31.

// -- Tire profiles (story 04) --
// The selector and all edit fields bind to TireProfiles globals. Since #14 the selector
// is TRANSIENT (EEPROM_NO_PERSIST): the active slot is always resolved from the current
// mode's default profile at boot and on every mode change, so persisting a "last profile"
// would only fight that. A manual pick here still takes effect immediately and holds
// until the next mode change or reboot.
//
// Since #15 every edit field below is TRANSIENT too -- they are never tree-walked to
// EEPROM. They used to be duplicated at bytes 113..121, but #15 grew TireProfile so three
// slots run past there. The duplicate is gone rather than relocated: the profile region
// already stores these byte-verbatim, so there was never anything worth persisting twice.
// Dropping it also spares the offset fields the menu path's "a VALUE_BYTE stored as 0 is
// ambiguous" history (see MenuSystem.cpp).
//
// #19: these bind DIRECTLY into the selected slot (g_profiles[g_profileSel]) -- there is no
// working copy any more. retargetProfileBindings() re-points them when the selection
// changes, so switching profiles only changes which slot the UI edits; every slot keeps its
// own pending edits, and root "Save Settings" writes them all. The initialisers below name
// slot 0 purely to start from a valid address (a link-time constant -- no static-init-order
// hazard); the first retarget happens before the menu can be drawn.
static MenuValueBinding profileSelectBinding = {
    VALUE_ENUM,
    &g_profileSel,
    nullptr,
    0,
    0,
    EEPROM_NO_PERSIST,
    g_profileNameLabels,
    PROFILE_COUNT
};
static MenuValueBinding profileWindowMinBinding = {
    VALUE_BYTE, &g_profiles[0].windowMin, nullptr, 0, 255, EEPROM_NO_PERSIST, nullptr, 0
};
static MenuValueBinding profileWindowIdealBinding = {
    VALUE_BYTE, &g_profiles[0].windowIdeal, nullptr, 0, 255, EEPROM_NO_PERSIST, nullptr, 0
};
static MenuValueBinding profileWindowMaxBinding = {
    VALUE_BYTE, &g_profiles[0].windowMax, nullptr, 0, 255, EEPROM_NO_PERSIST, nullptr, 0
};
static MenuValueBinding profileOffsetKBinding = {
    VALUE_BYTE, &g_profiles[0].offsetK, nullptr, 0, 80, EEPROM_NO_PERSIST, nullptr, 0
};
static MenuValueBinding profileTauBinding = {
    VALUE_BYTE, &g_profiles[0].tauSeconds, nullptr, 1, 60, EEPROM_NO_PERSIST, nullptr, 0
};
// Per-corner camera crop offsets (#15), corner order FL, FR, RL, RR. Same edit-buffer /
// transient treatment as the fields above; the range mirrors the old global offsets.
static MenuValueBinding profileLeftOffsetFLBinding = {
    VALUE_BYTE, &g_profiles[0].leftOffset[0], nullptr, 0, PROFILE_OFFSET_MAX, EEPROM_NO_PERSIST, nullptr, 0
};
static MenuValueBinding profileRightOffsetFLBinding = {
    VALUE_BYTE, &g_profiles[0].rightOffset[0], nullptr, 0, PROFILE_OFFSET_MAX, EEPROM_NO_PERSIST, nullptr, 0
};
static MenuValueBinding profileLeftOffsetFRBinding = {
    VALUE_BYTE, &g_profiles[0].leftOffset[1], nullptr, 0, PROFILE_OFFSET_MAX, EEPROM_NO_PERSIST, nullptr, 0
};
static MenuValueBinding profileRightOffsetFRBinding = {
    VALUE_BYTE, &g_profiles[0].rightOffset[1], nullptr, 0, PROFILE_OFFSET_MAX, EEPROM_NO_PERSIST, nullptr, 0
};
static MenuValueBinding profileLeftOffsetRLBinding = {
    VALUE_BYTE, &g_profiles[0].leftOffset[2], nullptr, 0, PROFILE_OFFSET_MAX, EEPROM_NO_PERSIST, nullptr, 0
};
static MenuValueBinding profileRightOffsetRLBinding = {
    VALUE_BYTE, &g_profiles[0].rightOffset[2], nullptr, 0, PROFILE_OFFSET_MAX, EEPROM_NO_PERSIST, nullptr, 0
};
static MenuValueBinding profileLeftOffsetRRBinding = {
    VALUE_BYTE, &g_profiles[0].leftOffset[3], nullptr, 0, PROFILE_OFFSET_MAX, EEPROM_NO_PERSIST, nullptr, 0
};
static MenuValueBinding profileRightOffsetRRBinding = {
    VALUE_BYTE, &g_profiles[0].rightOffset[3], nullptr, 0, PROFILE_OFFSET_MAX, EEPROM_NO_PERSIST, nullptr, 0
};

// ----------------------------------------------------
//  3) Submenu Item Arrays
// ----------------------------------------------------
// -- "Temperature": the two global decisions about what a temperature number IS (#22) --
// "Source" is the old root-level "Display" (Raw/Calculated). It was surfaced in both mode
// menus (#16), which read as a per-mode setting; it is neither per-mode NOR a display
// setting. It is one shared global byte, and per TempReader.h it REPLACES the working
// section temps with EMA_tau(surface)+K -- so the inflation verdict, the balance readout,
// session recording and the primary NBP channels all run on whichever signal is picked
// here. Filing it under "Display" would repeat exactly the mislabel this menu fixes.
// "Scale" is the old root-level "Temp Scale"; it is a pure unit conversion and is buried
// here because it is set once and never touched again.
static MenuItem temperatureMenu[] = {
    { "Source", MENU_VALUE, nullptr, nullptr, 0, &calcDisplayModeBinding  },
    { "Scale",  MENU_VALUE, nullptr, nullptr, 0, &temperatureScaleBinding }
};

// Balance summary action (defined in section 6). Opens the front/rear + left/right
// readout; Track-mode-only and honors the Show Balance toggle.
static void doShowBalance();
// Session summary recall action (story 01). Opens the last sealed summary; Track-only.
static void doViewSummary();

// Street's own tire temp window (#27) joins Default Profile here -- this is the "obvious
// home for the next per-mode setting" the #22 comment left room for, and the window is
// the one thing street genuinely wants to hold independently of whichever track-tuned
// profile happens to be active.
//
// "Override Window" leads the three values it governs: with it off they are inert and the
// active profile's window applies, which is the post-#14 behavior. Track Settings
// deliberately gets no equivalent -- on track the profile IS the window.
static MenuItem streetSettingsMenu[] = {
    { "Default Profile", MENU_VALUE, nullptr, nullptr, 0, &streetProfileBinding      },
    { "Override Window", MENU_VALUE, nullptr, nullptr, 0, &streetWindowEnabledBinding },
    { "Min",             MENU_VALUE, nullptr, nullptr, 0, &streetMinBinding          },
    { "Ideal",           MENU_VALUE, nullptr, nullptr, 0, &streetIdealBinding        },
    { "Max",             MENU_VALUE, nullptr, nullptr, 0, &streetMaxBinding          }
};

static MenuItem trackSettingsMenu[] = {
    { "Default Profile", MENU_VALUE, nullptr,      nullptr, 0, &trackProfileBinding    },
    { "Show Balance", MENU_VALUE,  nullptr,        nullptr, 0, &showBalanceBinding     },
    { "Balance",      MENU_ACTION, doShowBalance,  nullptr, 0, nullptr                 },
    { "View Summary", MENU_ACTION, doViewSummary,  nullptr, 0, nullptr                 },
    { "Auto-Seal",    MENU_VALUE,  nullptr,        nullptr, 0, &autoSealStationaryBinding }
};

static MenuItem modeSettingsMenu[] = {
    { "Street Settings", MENU_SUBMENU, nullptr, streetSettingsMenu, sizeof(streetSettingsMenu)/sizeof(MenuItem), nullptr },
    { "Track Settings",  MENU_SUBMENU, nullptr, trackSettingsMenu,  sizeof(trackSettingsMenu)/sizeof(MenuItem),  nullptr }
};

// -- "Straight-Line Gate": was "IMU Gate" (#22) --
// Renamed off the chip and onto the job. These four decide which frames are allowed to
// count at all, so they gate the INPUT to the verdict; they are set-up values (Orientation
// especially) rather than things tuned between sessions, which is why they sit one level
// below the thresholds instead of beside them.
//
// The two dwells are still NOT the same thing, and they are now deliberately on separate
// screens with names that say so: "Gate Dwell" here is how long the car must hold
// sub-threshold lateral g before capture STARTS; "Latch" on the parent screen is how long
// a verdict must hold on already-captured frames before it TRIPS. See the block comment on
// the backing variables.
static MenuItem straightLineGateMenu[] = {
    { "Gate Enable",     MENU_VALUE, nullptr, nullptr, 0, &imuGateEnabledBinding   },
    { "Lateral cg",      MENU_VALUE, nullptr, nullptr, 0, &lateralGateCentiGBinding },
    { "Gate Dwell 0.1s", MENU_VALUE, nullptr, nullptr, 0, &gateDwellTenthsBinding   },
    { "Orientation",     MENU_VALUE, nullptr, nullptr, 0, &imuOrientBinding         },
};

// -- "Inflation & Camber": one feature, one menu (#22) --
// These nine settings are a single pipeline -- thresholds -> straight-line gate -> latch ->
// paint it -- but they used to be split across "IMU Gate" (6) and "Camera Settings" (3),
// and not one of those three had anything to do with a camera. Named for the two things the
// check distinguishes: edge-vs-centre divergence is an inflation call, outer-vs-inner is a
// camber one. What you actually tune sits on this screen; the gate mechanics nest below.
static MenuItem inflationCamberMenu[] = {
    { "Segment Deltas",    MENU_VALUE, nullptr, nullptr, 0, &showSegmentDeltasBinding },
    { "Show G Bar",        MENU_VALUE, nullptr, nullptr, 0, &showGateBarBinding       },
    { "Inflation Delta %", MENU_VALUE, nullptr, nullptr, 0, &minInflationDeltaPctBinding },
    { "Alignment Delta %", MENU_VALUE, nullptr, nullptr, 0, &minAlignmentDeltaPctBinding },
    { "Latch 0.1s",        MENU_VALUE, nullptr, nullptr, 0, &alertDwellTenthsBinding  },
    { "Straight-Line Gate", MENU_SUBMENU, nullptr, straightLineGateMenu, sizeof(straightLineGateMenu)/sizeof(MenuItem), nullptr }
};

// -- "Display": what is left once the mislabelled items go home (#22) --
// The old "Camera Settings" was named for hardware and held three verdict settings that
// have moved to Inflation & Camber. What genuinely remains is presentation: how bright the
// screen is at night, how the thermal image is coloured, whether the crop guides are drawn
// over it, and how often the tire display repaints.
// Interactive lens setup action (#31), defined in section 6.
static void doSetCameraDegrees();

// The four lens items (#31) join it on the same "device-wide, so it lives here" rule that
// already put Show Offsets here rather than next to the per-profile offset values. They
// are not purely presentation -- the correction changes measured band temperatures, not
// just the picture -- but the root menu is an exact 9/9 fit against MenuRenderer's
// viewport and a 10th root item brings the scrollbar back, so a "Camera" root submenu
// would have to displace something.
//
// This menu is now 8 of 9 rows. The NEXT item added here brings the scrollbar back, at
// which point the four lens items should nest into a "Lens" submenu rather than anything
// being displaced.
static MenuItem displayMenu[] = {
    { "Night Brightness", MENU_VALUE, nullptr, nullptr, 0, &nightBrightnessBinding      },
    { "Thermal Gradient", MENU_VALUE, nullptr, nullptr, 0, &useThermalGradientBinding   },
    { "Show Offsets",     MENU_VALUE, nullptr, nullptr, 0, &showPixelOffsetsBinding     },
    { "Hi Freq Updates",  MENU_VALUE, nullptr, nullptr, 0, &highFrequencyUpdatesBinding },
    { "Lens Correct",     MENU_VALUE, nullptr, nullptr, 0, &lensCorrectEnabledBinding   },
    { "Camera Degrees",   MENU_VALUE, nullptr, nullptr, 0, &lensFovDegreesBinding       },
    { "Fit to View",      MENU_VALUE, nullptr, nullptr, 0, &lensFitToViewBinding        },
    { "Set Camera Degrees", MENU_ACTION, doSetCameraDegrees, nullptr, 0, nullptr        }
};

// Per-profile camera crop offsets (#15). Mirrors the corner / Left-Right shape the old
// global "Camera Settings" offsets had, so the tuning gestures are unchanged -- only the
// values now belong to the selected profile's edit buffer, saved by "Save Prof".
static MenuItem profileOffsetsFrontLeftMenu[] = {
    { "Left",  MENU_VALUE, nullptr, nullptr, 0, &profileLeftOffsetFLBinding  },
    { "Right", MENU_VALUE, nullptr, nullptr, 0, &profileRightOffsetFLBinding }
};

static MenuItem profileOffsetsFrontRightMenu[] = {
    { "Left",  MENU_VALUE, nullptr, nullptr, 0, &profileLeftOffsetFRBinding  },
    { "Right", MENU_VALUE, nullptr, nullptr, 0, &profileRightOffsetFRBinding }
};

static MenuItem profileOffsetsRearLeftMenu[] = {
    { "Left",  MENU_VALUE, nullptr, nullptr, 0, &profileLeftOffsetRLBinding  },
    { "Right", MENU_VALUE, nullptr, nullptr, 0, &profileRightOffsetRLBinding }
};

static MenuItem profileOffsetsRearRightMenu[] = {
    { "Left",  MENU_VALUE, nullptr, nullptr, 0, &profileLeftOffsetRRBinding  },
    { "Right", MENU_VALUE, nullptr, nullptr, 0, &profileRightOffsetRRBinding }
};

// Interactive setup action (#23), defined in section 6.
static void doSetOffsets();

// "Set Offsets" leads because it is the way these values are meant to be set: the eight
// numeric fields below it are a pixel aim, and this screen is the only one that shows you
// the picture you are aiming at. They stay for fine adjustment and for reading back what the
// mode left behind.
static MenuItem profileOffsetsMenu[] = {
    { "Set Offsets", MENU_ACTION, doSetOffsets, nullptr, 0, nullptr },
    { "Front Left",  MENU_SUBMENU, nullptr, profileOffsetsFrontLeftMenu,  sizeof(profileOffsetsFrontLeftMenu)/sizeof(MenuItem),  nullptr },
    { "Front Right", MENU_SUBMENU, nullptr, profileOffsetsFrontRightMenu, sizeof(profileOffsetsFrontRightMenu)/sizeof(MenuItem), nullptr },
    { "Rear Left",   MENU_SUBMENU, nullptr, profileOffsetsRearLeftMenu,   sizeof(profileOffsetsRearLeftMenu)/sizeof(MenuItem),   nullptr },
    { "Rear Right",  MENU_SUBMENU, nullptr, profileOffsetsRearRightMenu,  sizeof(profileOffsetsRearRightMenu)/sizeof(MenuItem),  nullptr }
};

// Tire-profile action callbacks (defined in section 6).
static void doNameProfile();
static void doResetProfile();

// No "Load" / "Save Prof" items (#18). The fields below edit the selected slot directly
// (#19), so there is nothing to load by hand; and the root menu's "Save Settings" writes
// all three slots, so a profile-only save was a strict subset of it -- and a misleading one
// once several profiles can hold pending edits at the same time. "Reset" stays -- reverting
// one slot to its seed is distinct.
static MenuItem tireProfilesMenu[] = {
    { "Profile",   MENU_VALUE,  nullptr,        nullptr, 0, &profileSelectBinding     },
    { "Name",      MENU_ACTION, doNameProfile,  nullptr, 0, nullptr                   },
    { "Min",       MENU_VALUE,  nullptr,        nullptr, 0, &profileWindowMinBinding  },
    { "Ideal",     MENU_VALUE,  nullptr,        nullptr, 0, &profileWindowIdealBinding},
    { "Max",       MENU_VALUE,  nullptr,        nullptr, 0, &profileWindowMaxBinding  },
    // Display names only (#17) -- the fields stay offsetK / tauSeconds in code. "\xF8" is
    // the CP437 degree ring; display.cp437(true) in setup() makes it render literally.
    { "Carcass Offset \xF8", MENU_VALUE, nullptr, nullptr, 0, &profileOffsetKBinding   },
    { "Carcass Lag s", MENU_VALUE,  nullptr,        nullptr, 0, &profileTauBinding     },
    { "Offsets",   MENU_SUBMENU, nullptr, profileOffsetsMenu, sizeof(profileOffsetsMenu)/sizeof(MenuItem), nullptr },
    { "Reset",     MENU_ACTION, doResetProfile, nullptr, 0, nullptr                   },
};

// ----------------------------------------------------
//  4) Save/Load Action Callbacks
// ----------------------------------------------------
static void doSave();
static void doLoad();

// ----------------------------------------------------
//  5) Main Menu Definition (with Save/Load items)
// ----------------------------------------------------
// Root menu (#22). Exactly 9 items against MenuRenderer's 9-row viewport
// ((240 - 22 status strip - 30 top margin) / 20), so it fills the screen without
// scrolling -- it was 11, and scrolled. That is an exact fit with no headroom: a 10th
// root item brings the scrollbar back, so anything added later has to displace something
// or nest. Grouped on one rule -- no menu is named after the hardware it happens to use --
// which is why "Camera Settings", "IMU Gate" and "Hardware Settings" are all gone.
//
// "Current Tire" is a second item pointing at the SAME profileSelectBinding as
// Tire Profiles -> Profile, hoisted to the root so swapping tires is one tap. It needs no
// supporting code: serviceProfileEditSync() polls g_profileSel from loop() rather than
// hooking a particular menu item, so it fires whichever of the two wrote it. The binding is
// EEPROM_NO_PERSIST, so the duplicate reference cannot double-write.
static MenuItem mainMenu[] = {
    {
      "Current Mode",
      MENU_VALUE,
      nullptr,
      nullptr,
      0,
      &currentModeBinding
    },
    {
      "Current Tire",
      MENU_VALUE,
      nullptr,
      nullptr,
      0,
      &profileSelectBinding
    },
    {
      "Temperature",
      MENU_SUBMENU,
      nullptr,
      temperatureMenu,
      sizeof(temperatureMenu)/sizeof(MenuItem),
      nullptr
    },
    {
      "Mode Settings",
      MENU_SUBMENU,
      nullptr,
      modeSettingsMenu,
      sizeof(modeSettingsMenu)/sizeof(MenuItem),
      nullptr
    },
    {
      "Tire Profiles",
      MENU_SUBMENU,
      nullptr,
      tireProfilesMenu,
      sizeof(tireProfilesMenu)/sizeof(MenuItem),
      nullptr
    },
    {
      "Inflation & Camber",
      MENU_SUBMENU,
      nullptr,
      inflationCamberMenu,
      sizeof(inflationCamberMenu)/sizeof(MenuItem),
      nullptr
    },
    {
      "Display",
      MENU_SUBMENU,
      nullptr,
      displayMenu,
      sizeof(displayMenu)/sizeof(MenuItem),
      nullptr
    },
    {
        "Test",
        MENU_VALUE,
        nullptr,
        nullptr,
        0,
        &testEnabledBinding
    },
    {
      "Save Config",
      MENU_ACTION,
      doSave,
      nullptr,
      0,
      nullptr
    }
};

// We create a global MenuSystem instance for all items
static MenuSystem tireMenuSystem(
    mainMenu,
    sizeof(mainMenu)/sizeof(MenuItem)
);

// ----------------------------------------------------
//  6) Implementation of the Save/Load callbacks
// ----------------------------------------------------
static void doSave()
{
    tireMenuSystem.saveToEEPROM();
    // Persist tire profiles alongside the menu settings so one "Save Settings" covers
    // everything. Since #19 the edit fields write straight into their slot, so there is
    // nothing to commit first -- this writes EVERY slot, which is what makes edits to
    // several profiles in one visit all survive a single save.
    TireProfiles::save();
    // Provide visual feedback
    menuRenderer.setStatusMessage("Settings Saved!");
    // Force a re-render if you want immediate update
    menuRenderer.render();
}

static void doLoad()
{
    tireMenuSystem.loadFromEEPROM();
    TireProfiles::begin();
    // The active slot is transient: resolve it from the mode we just loaded (#14).
    applyModeDefaultProfile();
}

static void retargetProfileBindings(uint8_t slot);

// -- Mode -> default tire profile (#14) --
// The mode picks which profile is active; the profile is the single source of truth for
// the temp window. Runs at boot and on every mode change, so the window always matches
// the mode's default profile without anything being persisted per-boot.
void applyModeDefaultProfile()
{
    uint8_t sel = (currentMode == 1) ? trackProfile : streetProfile;
    if (sel >= PROFILE_COUNT) sel = 0;   // guard against a stale/garbage stored index
    g_profileSel = sel;
    // Point the Tire Profiles edit fields at the slot we just adopted, so they show the
    // profile that is actually driving the display (#19).
    retargetProfileBindings(sel);
}

// -- Profile selector -> which slot the edit fields point at (#19) --
// No data is copied: the bindings are re-pointed at the selected slot's storage, so each
// profile keeps its own pending edits and one "Save Settings" persists them all. Switching
// profiles is purely a change of view.
static void retargetProfileBindings(uint8_t slot)
{
    if (slot >= PROFILE_COUNT) slot = 0;
    TireProfile& p = g_profiles[slot];

    profileWindowMinBinding.valuePtr   = &p.windowMin;
    profileWindowIdealBinding.valuePtr = &p.windowIdeal;
    profileWindowMaxBinding.valuePtr   = &p.windowMax;
    profileOffsetKBinding.valuePtr     = &p.offsetK;
    profileTauBinding.valuePtr         = &p.tauSeconds;

    profileLeftOffsetFLBinding.valuePtr  = &p.leftOffset[0];
    profileRightOffsetFLBinding.valuePtr = &p.rightOffset[0];
    profileLeftOffsetFRBinding.valuePtr  = &p.leftOffset[1];
    profileRightOffsetFRBinding.valuePtr = &p.rightOffset[1];
    profileLeftOffsetRLBinding.valuePtr  = &p.leftOffset[2];
    profileRightOffsetRLBinding.valuePtr = &p.rightOffset[2];
    profileLeftOffsetRRBinding.valuePtr  = &p.leftOffset[3];
    profileRightOffsetRRBinding.valuePtr = &p.rightOffset[3];
}

// MenuValueBinding carries no change-callback, so moving the "Profile" item only updates
// g_profileSel -- nothing would otherwise notice. Watching it here is what makes the
// selector work at all (and is why the old manual "Load" item could go away in #18).
// Called from loop() alongside serviceModeProfileSnap(), so it also fires while the menu is
// open. Idempotent; applyModeDefaultProfile() retargets too, and a repeat is a no-op.
void serviceProfileEditSync()
{
    static uint8_t lastSel = 0xFF;      // 0xFF forces a retarget on the first call
    if (g_profileSel == lastSel) return;
    lastSel = g_profileSel;
    retargetProfileBindings(g_profileSel);
}

// -- Tire-profile actions (story 04) --
static void doNameProfile()
{
    // Hand off to the small-screen name editor (swipe up/down = letter, left = lock).
    menuRenderer.beginNameEdit(g_profiles[TireProfiles::activeIndex()].name, PROFILE_NAME_LEN);
}

static void doResetProfile()
{
    TireProfiles::resetSelectedToDefault();
    menuRenderer.setStatusMessage("Profile reset");
}

// -- Interactive camera offset setup (#23) --
// Raised here, acted on in loop(). An action callback runs several frames deep inside the
// gesture handler -- it cannot close the menu, and it must not start a mode that draws over
// the screen the handler is about to re-render. So it just asks, and the sketch (which is
// also where the reader gets rebuilt on menu close) does the real work.
static bool offsetSetupRequested = false;

static void doSetOffsets()
{
    // Nothing to aim without a camera: every corner is a single-point sensor, so there is no
    // image to put a crop guide on. Say so rather than opening a black screen.
    if (!OffsetSetup::hasEditableTargets(tempReader)) {
        menuRenderer.setStatusMessage("No cameras");
        return;
    }
    offsetSetupRequested = true;
}

bool consumeOffsetSetupRequest()
{
    bool requested = offsetSetupRequested;
    offsetSetupRequested = false;
    return requested;
}

// -- Interactive camera field-of-view setup (#31) --
// Same request/consume shape as Set Offsets above, and for the same reason: an action
// callback runs several frames deep inside the gesture handler, where it can neither close
// the menu nor start a mode that draws over the screen the handler is about to re-render.
static bool lensSetupRequested = false;

static void doSetCameraDegrees()
{
    // Nothing to judge without a camera image -- every corner is a single-point sensor, so
    // there are no grooves to straighten. Say so rather than opening a black screen.
    if (!LensSetup::hasEditableTargets(tempReader)) {
        menuRenderer.setStatusMessage("No cameras");
        return;
    }
    // Tuning a correction that is switched off would be swiping at a raw image and
    // wondering why nothing moves.
    if (!lensCorrectEnabled) {
        menuRenderer.setStatusMessage("Lens Correct off");
        return;
    }
    lensSetupRequested = true;
}

bool consumeLensSetupRequest()
{
    bool requested = lensSetupRequested;
    lensSetupRequested = false;
    return requested;
}

// The interactive mode is another editor for the same byte the "Camera Degrees" field
// edits, so it reads and writes it through here rather than keeping a copy.
uint8_t getLensFovDegrees()   { return lensFovDegrees; }
void    setLensFovDegrees(uint8_t v) { lensFovDegrees = v; }
bool    getLensCorrectEnabled() { return lensCorrectEnabled; }
bool    getLensFitToView()      { return lensFitToView; }

// -- Balance summary action (story 05) --
static void doShowBalance()
{
    // Track-mode-only feature: inert in Street mode.
    if (currentMode != 1) {
        menuRenderer.setStatusMessage("Track mode only");
        return;
    }
    // Respect the show/hide setting.
    if (!showBalance) {
        menuRenderer.setStatusMessage("Balance hidden");
        return;
    }
    // Hand off to the full-screen readout; the touch loop re-renders it and any gesture
    // returns to the menu.
    menuRenderer.showBalance();
}

// -- Session summary recall action (story 01) --
static void doViewSummary()
{
    // Track-mode-only feature: inert in Street mode.
    if (currentMode != 1) {
        menuRenderer.setStatusMessage("Track mode only");
        return;
    }
    // Full-screen multi-page recall; the touch loop pages/dismisses it.
    menuRenderer.showSummary();
}

// ----------------------------------------------------
//  7) Provide global access to the Tire MenuSystem
// ----------------------------------------------------
MenuSystem& getTireMenuSystem()
{
    return tireMenuSystem;
}

// Extern getters for the values, so the main sketch can read them
uint8_t getCurrentModeValue() {
    return currentMode;
}

uint8_t getTemperatureScaleValue() {
    return temperatureScale;
}

uint8_t getNightBrightness() {
    return nightBrightness;
}

bool getUseThermalGradient() {
    return useThermalGradient;
}

bool getTestEnabled() {
    return testEnabled;
}

// Per-mode default profile (#14). The sketch does not need these -- it reads the resolved
// active profile -- but they keep the settings readable for logging/diagnostics.
uint8_t getStreetProfile() {
    return streetProfile;
}

uint8_t getTrackProfile() {
    return trackProfile;
}

// Street tire temp window (#27). Read by the sketch's resolveTireWindow(), which is what
// initializeSystem() and sendBootMetadata() both go through -- in Street mode with the
// override on these replace the active profile's window everywhere it is consumed (thermal
// thresholds, the Wheels tire map, and therefore any session started from it). Raw F-seed
// bytes, exactly like TireProfile.window*; unit conversion happens downstream.
bool getStreetWindowEnabled() {
    return streetWindowEnabled;
}

uint8_t getStreetMin() {
    return streetMin;
}

uint8_t getStreetIdeal() {
    return streetIdeal;
}

uint8_t getStreetMax() {
    return streetMax;
}

uint8_t getCalcDisplayMode() {
    return calcDisplayMode;
}

bool getShowBalance() {
    return showBalance;
}

bool getAutoSealStationary() {
    return autoSealStationary;
}

bool getShowPixelOffsets() {
    return showPixelOffsets;
}

bool getHighFrequencyUpdates() {
    return highFrequencyUpdates;
}

bool getShowSegmentDeltas() {
    return showSegmentDeltas;
}

uint8_t getminInflationDeltaPct() {
    return minInflationDeltaPct;
}

uint8_t getminAlignmentDeltaPct() {
    return minAlignmentDeltaPct;
}

bool getImuGateEnabled() {
    return imuGateEnabled;
}

bool getShowGateBar() {
    return showGateBar;
}

uint8_t getLateralGateCentiG() {
    return lateralGateCentiG;
}

uint8_t getGateDwellTenths() {
    return gateDwellTenths;
}

uint8_t getAlertDwellTenths() {
    return alertDwellTenths;
}

uint8_t getImuOrient() {
    return imuOrient;
}

// Camera crop offsets, per corner (0=FL, 1=FR, 2=RL, 3=RR). Since #15 these resolve
// against the ACTIVE tire profile rather than eight globals, so switching profiles swaps
// the crop along with the window / K / tau. Signatures are unchanged on purpose: the
// consumers (tires_esp32.ino -> TempReader, ThermalDisplay, NBP boot metadata) still read
// them exactly as before, and initializeSystem() re-pushes them whenever the menu closes,
// which is also when a profile change takes effect.
byte getLeftPixelOffset(int index){
    if (index < 0 || index >= 4) return 0;
    return TireProfiles::active().leftOffset[index];
}

byte getRightPixelOffset(int index){
    if (index < 0 || index >= 4) return 0;
    return TireProfiles::active().rightOffset[index];
}
