hydroslide/tires_monitor/tires_esp32/TouchMenuHandler.cpp

#include "TouchMenuHandler.h"
//#include "CST816Touch.h"

extern HWCDC USBSerial;

TouchMenuHandler::TouchMenuHandler(MenuSystem& menuSystem, MenuRenderer& renderer, CST816Touch& touch)
: menu(menuSystem), render(renderer), touchSensor(touch)
{
}

bool TouchMenuHandler::isMenuActive(){
    return menuActive;
}

bool TouchMenuHandler::SwipedRight(){
    bool temp = unhandledSwipeRight;
    unhandledSwipeRight=false;
    return temp;
}
bool TouchMenuHandler::SwipedUp(){
    bool temp = unhandledSwipeUp;
    unhandledSwipeUp=false;
    return temp;
}
bool TouchMenuHandler::SwipedDown(){
    bool temp = unhandledSwipeDown;
    unhandledSwipeDown=false;
    return temp;
}
bool TouchMenuHandler::SwipedLeft(){
    bool temp = unhandledSwipeLeft;
    unhandledSwipeLeft=false;
    return temp;
}

void TouchMenuHandler::suspendMenu(bool suspend){
    menuSuspended = suspend;
}

void TouchMenuHandler::openMenu(){
    menuActive = true;
    // Paint immediately rather than waiting for the next gesture: loop() only re-renders
    // after it has handled one, so without this the screen would keep whatever the mode we
    // just came back from left on it.
    render.render();
}

void TouchMenuHandler::closeMenu(){
    menuActive = false;
}

void TouchMenuHandler::loop(int timeDelta) {
    // Poll the touch sensor
    touchSensor.control();

    TouchScreenEventCache* pTouchCache = TouchScreenEventCache::getInstance();
	
    lastTouchDelta+=timeDelta;

    TouchScreenController::gesture_t gesture = TouchScreenController::gesture_t::GESTURE_NONE;
	if (pTouchCache->hadGesture()) {
		int x = 0;
        int y = 0; 
        pTouchCache->getLastGesture(gesture, x, y);	//this 'consumes' the gesture from the event cache
        if (lastTouchDelta>= touchDelay){
            lastTouchDelta=0;        
          
            USBSerial.print("Gesture: ");
            USBSerial.print(TouchScreenController::gestureIdToString(gesture));
            if ((gesture == TouchScreenController::gesture_t::GESTURE_DOUBLE_CLICK) || (gesture == TouchScreenController::gesture_t::GESTURE_LONG_PRESS)) {
                USBSerial.print(", at position (");
                USBSerial.print(x);
                USBSerial.print(", ");
                USBSerial.print(y);
                USBSerial.print(")");
            }
            USBSerial.println("");
        }
        else
            gesture = TouchScreenController::gesture_t::GESTURE_NONE;
	}



    if (gesture == TouchScreenController::gesture_t::GESTURE_NONE) {
        // No new gesture
        return;
    }

    // Handle the gesture
    handleGesture(gesture);

    if (menuActive){
        // After handling, re-render
        render.render();
    }
}

void TouchMenuHandler::handleGesture(TouchScreenController::gesture_t gesture) {
    MenuRenderState &rState = render.getState();

    unhandledSwipeDown=false;
    unhandledSwipeRight=false;
    unhandledSwipeLeft=false;
    unhandledSwipeUp=false;
   
    // Session summary screen (story 01) takes over the whole screen; up/down page
    // through it, any other gesture dismisses it and returns to the menu.
    if (menuActive && rState.summaryViewing) {
        if (gesture == TouchScreenController::gesture_t::GESTURE_UP)
            render.summaryPageStep(+1);
        else if (gesture == TouchScreenController::gesture_t::GESTURE_DOWN)
            render.summaryPageStep(-1);
        else
            render.exitSummary();
        return;
    }

    // Balance summary screen (story 05) takes over the whole screen; any gesture
    // dismisses it and returns to the menu.
    if (menuActive && rState.balanceViewing) {
        render.exitBalance();
        return;
    }

    // Name-entry mode intercepts navigation: up/down cycle the current letter, left
    // (or a tap) advances a slot (past the last slot saves & exits), right retreats a
    // slot (swiping right past the first slot cancels), a double-click cancels. Left is
    // the confirm swipe and right is the back swipe here so the editor matches the rest
    // of the menu (left selects/descends, right goes back). Story 04.
    if (menuActive && rState.nameEditing) {
        switch (gesture) {
        case TouchScreenController::gesture_t::GESTURE_UP:
            render.nameCycle(+1);
            break;
        case TouchScreenController::gesture_t::GESTURE_DOWN:
            render.nameCycle(-1);
            break;
        case TouchScreenController::gesture_t::GESTURE_LEFT:
        case TouchScreenController::gesture_t::GESTURE_TOUCH_BUTTON:
            // next slot (rightward through the name); past the last slot commits/saves
            render.nameAdvance();
            break;
        case TouchScreenController::gesture_t::GESTURE_RIGHT:
            // previous slot (leftward); past the first slot backs out of the edit
            render.nameRetreat();
            break;
        case TouchScreenController::gesture_t::GESTURE_DOUBLE_CLICK:
        case TouchScreenController::gesture_t::GESTURE_LONG_PRESS:
            render.nameCancel();
            break;
        default:
            break;
        }
        return;
    }

    if (!menuActive){
        if (gesture == TouchScreenController::gesture_t::GESTURE_LEFT){
            // Left is normally the "open the menu" swipe and never reaches the sketch. A
            // suspended menu hands it over instead, which is what lets offset setup (#23)
            // use both horizontal directions to walk a guide line.
            if (menuSuspended) unhandledSwipeLeft = true;
            else               menuActive = true;
        }
        else if(gesture == TouchScreenController::gesture_t::GESTURE_RIGHT)
            unhandledSwipeRight=true;
        else if(gesture == TouchScreenController::gesture_t::GESTURE_UP)
            unhandledSwipeUp=true;
        else if(gesture == TouchScreenController::gesture_t::GESTURE_DOWN)
            unhandledSwipeDown=true;
        return;
    }

    switch (gesture) {
    case TouchScreenController::gesture_t::GESTURE_UP:
        if (!rState.dropdownOpen && !rState.numericEditing) {
            // Normal menu navigation up
            menu.previousItem();
        } else if (rState.dropdownOpen) {
            // Move up in dropdown
            render.dropdownUp();
        } else if (rState.numericEditing) {
            // Increase numeric value
            menu.increaseValue();
        }
        break;

    case TouchScreenController::gesture_t::GESTURE_DOWN:
        if (!rState.dropdownOpen && !rState.numericEditing) {
            // Normal menu navigation down
            menu.nextItem();
        } else if (rState.dropdownOpen) {
            // Move down in dropdown
            render.dropdownDown();
        } else if (rState.numericEditing) {
            // Decrease numeric value
            menu.decreaseValue();
        }
        break;

    case TouchScreenController::gesture_t::GESTURE_RIGHT:
        // If numeric editing or a dropdown is open, exit that mode
        if (rState.numericEditing) {
            rState.numericEditing = false;
        } else if (rState.dropdownOpen) {
            // Close the dropdown
            render.closeDropdown();
        } else {
            // Go back one level in the menu
           if (!menu.goBack()){
                menuActive=false;
                return;
           }
        }
        break;

    case TouchScreenController::gesture_t::GESTURE_LEFT:
    case TouchScreenController::gesture_t::GESTURE_TOUCH_BUTTON:
        if (rState.dropdownOpen) {
            // If user single-taps while dropdown is open, select
            render.selectDropdownValue();
        } else if (rState.numericEditing) {
            // Tapping while numeric editing - no special action by default
        } else {
            // Not editing anything, interpret tap as 'select' for the current menu item
            const MenuItem* currentItem = menu.getCurrentItem();
            if (!currentItem) break;

            if (currentItem->itemType == MENU_VALUE && currentItem->binding) {
                switch (currentItem->binding->valueType) {
                case VALUE_BOOL: {
                    // Toggle on single tap
                    bool* val = (bool*)currentItem->binding->valuePtr;
                    *val = !(*val);
                    break;
                }
                case VALUE_ENUM: {
                    // Open dropdown for an enum
                    uint8_t currentEnumVal = *(uint8_t*)currentItem->binding->valuePtr;
                    render.openDropdown(currentItem, currentEnumVal);
                    break;
                }
                case VALUE_BYTE:
                case VALUE_SBYTE: {
                    // Enter numeric editing mode
                    rState.numericEditing = true;
                    break;
                }
                case VALUE_STRING:
                    // Could open a keyboard or do nothing
                    break;
                }
            }
            else if (currentItem->itemType == MENU_ACTION) {
                // Execute the action
                menu.selectItem();
            }
            else if (currentItem->itemType == MENU_SUBMENU) {
                // Go deeper
                menu.selectItem();
            }
        }
        break;

    case TouchScreenController::gesture_t::GESTURE_DOUBLE_CLICK:
    case TouchScreenController::gesture_t::GESTURE_LONG_PRESS:
        // Not specified, ignoring or for advanced features
        break;

    case TouchScreenController::gesture_t::GESTURE_NONE:
    default:
        // No action
        break;
    }
}
