hydroslide/tires_monitor/menu_test/menu_test.ino

/*
  Basic menu example using GEM library. Using rotary encoder as an input source.

  Simple two page menu with one editable menu item associated with int variable, one with bool variable,
  and a button, pressing of which will result in int variable value printed to Serial monitor if bool variable is set to true.

  Second menu page with option select is added to better demonstrate operation of the menu with rotary encoder.

  Adafruit GFX library is used to draw menu.
  KeyDetector library (version 1.2.0 or later) is used to detect rotary encoder operation.
  
  Additional info (including the breadboard view) available on GitHub:
  https://github.com/Spirik/GEM
  
  This example code is in the public domain.
*/

#include <GEM_adafruit_gfx.h>
#include <KeyDetector.h>

// SPI and I2C libraries required by SH1106 display
//#include <SPI.h>
#include <Wire.h>
#include <Adafruit_GFX.h>

// Hardware-specific library for ST7789.
// Include library that matches your setup (see https://learn.adafruit.com/adafruit-gfx-graphics-library for details)
#include <Adafruit_ST7789.h> // Hardware-specific library for ST7789

// Define signal identifiers for three outputs of encoder (channel A, channel B and a push-button)
#define KEY_A 1
#define KEY_B 2
#define KEY_C 3

// Pins encoder is connected to
const byte channelA = 6;
const byte channelB = 5;
const byte buttonPin = 2;

byte chanB = HIGH; // Variable to store Channel B readings

// Array of Key objects that will link GEM key identifiers with dedicated pins
// (it is only necessary to detect signal change on a single channel of the encoder, either A or B;
// order of the channel and push-button Key objects in an array is not important)
Key keys[] = {{KEY_A, channelA}, {KEY_C, buttonPin}};
//Key keys[] = {{KEY_C, buttonPin}, {KEY_A, channelA}};

// Create KeyDetector object
// KeyDetector myKeyDetector(keys, sizeof(keys)/sizeof(Key));
// To account for switch bounce effect of the buttons (if occur) you may want to specify debounceDelay
// as the third argument to KeyDetector constructor.
// Make sure to adjust debounce delay to better fit your rotary encoder.
// Also it is possible to enable pull-up mode when buttons wired with pull-up resistors (as in this case).
// Analog threshold is not necessary for this example and is set to default value 16.
KeyDetector myKeyDetector(keys, sizeof(keys)/sizeof(Key), /* debounceDelay= */ 5, /* analogThreshold= */ 16, /* pullup= */ true);

bool secondaryPressed = false;  // If encoder rotated while key was being pressed; used to prevent unwanted triggers
bool cancelPressed = false;  // Flag indicating that Cancel action was triggered, used to prevent it from triggering multiple times
const int keyPressDelay = 1000; // How long to hold key in pressed state to trigger Cancel action, ms
long keyPressTime = 0; // Variable to hold time of the key press event
long now; // Variable to hold current time taken with millis() function at the beginning of loop()



#define TFT_CS 10
#define TFT_RST 8
#define TFT_DC 7

Adafruit_ST7789 tft = Adafruit_ST7789(TFT_CS, TFT_DC, TFT_RST);


// Create variables that will be editable through the menu and assign them initial values
byte minTemp=100;
byte idealTemp= 120;
byte maxTemp = 180;
bool useFarenheit = true;

// Create variable that will be editable through option select and create associated option select.
// This variable will be passed to menu.invertKeysDuringEdit(), and naturally can be presented as a bool,
// but is declared as a byte type to be used in an option select rather than checkbox (for demonstration purposes)
byte invert = 1;
SelectOptionByte selectInvertOptions[] = {{"Invert", 1}, {"Normal", 0}};
GEMSelect selectInvert(sizeof(selectInvertOptions)/sizeof(SelectOptionByte), selectInvertOptions);

// Create menu item for option select with applyInvert() callback function
void applyInvert(); // Forward declaration
GEMItem menuItemInvert("Chars order:", invert, selectInvert, applyInvert);


GEMSpinnerBoundariesByte spinnerByteBoundaries = { .step = 1, .min = 30, .max = 200 };
GEMSpinner spinnerByte(spinnerByteBoundaries);

void saveCallback(GEMCallbackData callbackData); // Forward declaration of optional callback

// Create two menu item objects of class GEMItem, linked to number and enablePrint variables 
GEMItem menuItemMinTemp("Min Temp:", minTemp, spinnerByte, saveCallback, GEM_VAL_BYTE);
GEMItem menuItemIdealTemp("Ideal Temp:", idealTemp, spinnerByte, saveCallback, GEM_VAL_BYTE);
GEMItem menuItemMaxTemp("Max Temp:", maxTemp, spinnerByte, saveCallback, GEM_VAL_BYTE);
GEMItem menuItemFarenheit("Farenheit:", useFarenheit);

// Create menu button that will trigger printData() function. It will print value of our number variable
// to Serial monitor if enablePrint is true. We will write (define) this function later. However, we should
// forward-declare it in order to pass to GEMItem constructor
void saveSettings(); // Forward declaration
GEMItem menuItemButton("Save Settings", saveSettings);

// Create menu page object of class GEMPage. Menu page holds menu items (GEMItem) and represents menu level.
// Menu can have multiple menu pages (linked to each other) with multiple menu items each
GEMPage menuPageMain("Main Menu"); // Main page
GEMPage menuPageSettings("Settings"); // Settings submenu

// Create menu item linked to Settings menu page
GEMItem menuItemMainSettings("Settings", menuPageSettings);

// Create menu object of class GEM_adafruit_gfx. Supply its constructor with reference to display object we created earlier
GEM_adafruit_gfx menu(tft, GEM_POINTER_ROW, GEM_ITEMS_COUNT_AUTO, 30,40,160);
// Which is equivalent to the following call (you can adjust parameters to better fit your screen if necessary):
// GEM_adafruit_gfx menu(display, /* menuPointerType= */ GEM_POINTER_ROW, /* menuItemsPerScreen= */ GEM_ITEMS_COUNT_AUTO, /* menuItemHeight= */ 10, /* menuPageScreenTopOffset= */ 10, /* menuValuesLeftOffset= */ 86);

void setup() {
tft.init(240, 280); // Init ST7789 280x240

tft.setRotation(1);
tft.fillScreen(ST77XX_BLACK);

  // Pin modes
  pinMode(channelA, INPUT_PULLUP);
  pinMode(channelB, INPUT_PULLUP);
  pinMode(buttonPin, INPUT_PULLUP);

  // Serial communication setup
  Serial.begin(9600);

  // Show image buffer on the display hardware.
  // Since the buffer is intialized with an Adafruit splashscreen
  // internally, this will display the splashscreen.
  delay(250);                       // Wait for the OLED to power up

  


  // Explicitly set correct colors for monochrome OLED screen
  menu.setForegroundColor(ST77XX_YELLOW);
  menu.setBackgroundColor(ST77XX_BLUE);

  // Disable GEM splash (it won't be visible on the screen of buffer-equiped displays such as this one any way)
  menu.setSplashDelay(0);
  
  // Turn inverted order of characters during edit mode on (feels more natural when using encoder)
  menu.invertKeysDuringEdit(invert);
  
  menu.setTextSize(2);
  menu.setSpriteSize(2);

  // Menu init, setup and draw
  menu.init();
  setupMenu();
  menu.drawMenu();

  
  //Serial.println("Initialized");
}

void setupMenu() {
  // Add menu items to Settings menu page
  menuPageSettings.addMenuItem(menuItemInvert);

  // Add menu items to menu page
  menuPageMain.addMenuItem(menuItemMainSettings);
  menuPageMain.addMenuItem(menuItemMinTemp);
  menuPageMain.addMenuItem(menuItemIdealTemp);
  menuPageMain.addMenuItem(menuItemMaxTemp);
  menuPageMain.addMenuItem(menuItemFarenheit);
  menuPageMain.addMenuItem(menuItemButton);

  // Specify parent menu page for the Settings menu page
  menuPageSettings.setParentMenuPage(menuPageMain);

  // Add menu page to menu and set it as current
  menu.setMenuPageCurrent(menuPageMain);
}

void loop() {
  // Get current time to use later on
  now = millis();

  // If menu is ready to accept button press...
  if (menu.readyForKey()) {
    chanB = digitalRead(channelB); // Reading Channel B signal beforehand to account for possible delays due to polling nature of KeyDetector algorithm
    // ...detect key press using KeyDetector library
    // and pass pressed button to menu
    myKeyDetector.detect();
  
    switch (myKeyDetector.trigger) {
      case KEY_A:
        // Signal from Channel A of encoder was detected
        if (chanB == LOW) {
          // If channel B is low then the knob was rotated CCW
          if (myKeyDetector.current == KEY_C) {
            // If push-button was pressed at that time, then treat this action as GEM_KEY_LEFT,...
            Serial.println("Rotation CCW with button pressed");
            menu.registerKeyPress(GEM_KEY_LEFT);
            // Button was in a pressed state during rotation of the knob, acting as a modifier to rotation action
            secondaryPressed = true;
          } else {
            // ...or GEM_KEY_UP otherwise
            Serial.println("Rotation CCW");
            menu.registerKeyPress(GEM_KEY_UP);
          }
        } else {
          // If channel B is high then the knob was rotated CW
          if (myKeyDetector.current == KEY_C) {
            // If push-button was pressed at that time, then treat this action as GEM_KEY_RIGHT,...
            Serial.println("Rotation CW with button pressed");
            menu.registerKeyPress(GEM_KEY_RIGHT);
            // Button was in a pressed state during rotation of the knob, acting as a modifier to rotation action
            secondaryPressed = true;
          } else {
            // ...or GEM_KEY_DOWN otherwise
            Serial.println("Rotation CW");
            menu.registerKeyPress(GEM_KEY_DOWN);
          }
        }
        break;
      case KEY_C:
        // Button was pressed
        Serial.println("Button pressed");
        // Save current time as a time of the key press event
        keyPressTime = now;
        break;
    }
    switch (myKeyDetector.triggerRelease) {
      case KEY_C:
        // Button was released
        Serial.println("Button released");
        if (!secondaryPressed) {
          // If button was not used as a modifier to rotation action...
          if (now <= keyPressTime + keyPressDelay) {
            // ...and if not enough time passed since keyPressTime,
            // treat key that was pressed as Ok button
            menu.registerKeyPress(GEM_KEY_OK);
          }
        }
        secondaryPressed = false;
        cancelPressed = false;
        break;
    }
    // After keyPressDelay passed since keyPressTime
    if (now > keyPressTime + keyPressDelay) {
      switch (myKeyDetector.current) {
        case KEY_C:
          if (!secondaryPressed && !cancelPressed) {
            // If button was not used as a modifier to rotation action, and Cancel action was not triggered yet
            Serial.println("Button remained pressed");
            // Treat key that was pressed as Cancel button
            menu.registerKeyPress(GEM_KEY_CANCEL);
            cancelPressed = true;
          }
          break;
      }
    }
    

  }
}

void saveSettings(){
  // Do Nothing
}

void saveCallback(GEMCallbackData callbackData) {
  // Print variable to Serial
  Serial.print("Selected value: ");
  /*
  switch (callbackData.valInt) {
    case GEM_VAL_BYTE:
        Serial.println(byteNumber);
        break;
      case GEM_VAL_INTEGER:
        Serial.println(intNumber);
        break;
      case GEM_VAL_FLOAT:
        Serial.println(floatNumber);
        break;
      case GEM_VAL_DOUBLE:
        Serial.println(doubleNumber);
        break;
  }
  */
}

void applyInvert() {
  menu.invertKeysDuringEdit(invert);
  // Print invert variable to Serial
  Serial.print("Invert: ");
  Serial.println(invert);
}
